YangXiao69/WSPS-325-150K-PEFA/接线图/并柜控制单元/WS2.016.289.V01 WSPS-325-150K-PEFA并柜控制单元接线图 表/WSPS-325-150K-PEFA并柜控制单元接线图.pdf

RPD OPD | DB9 | DB9

J1 J2

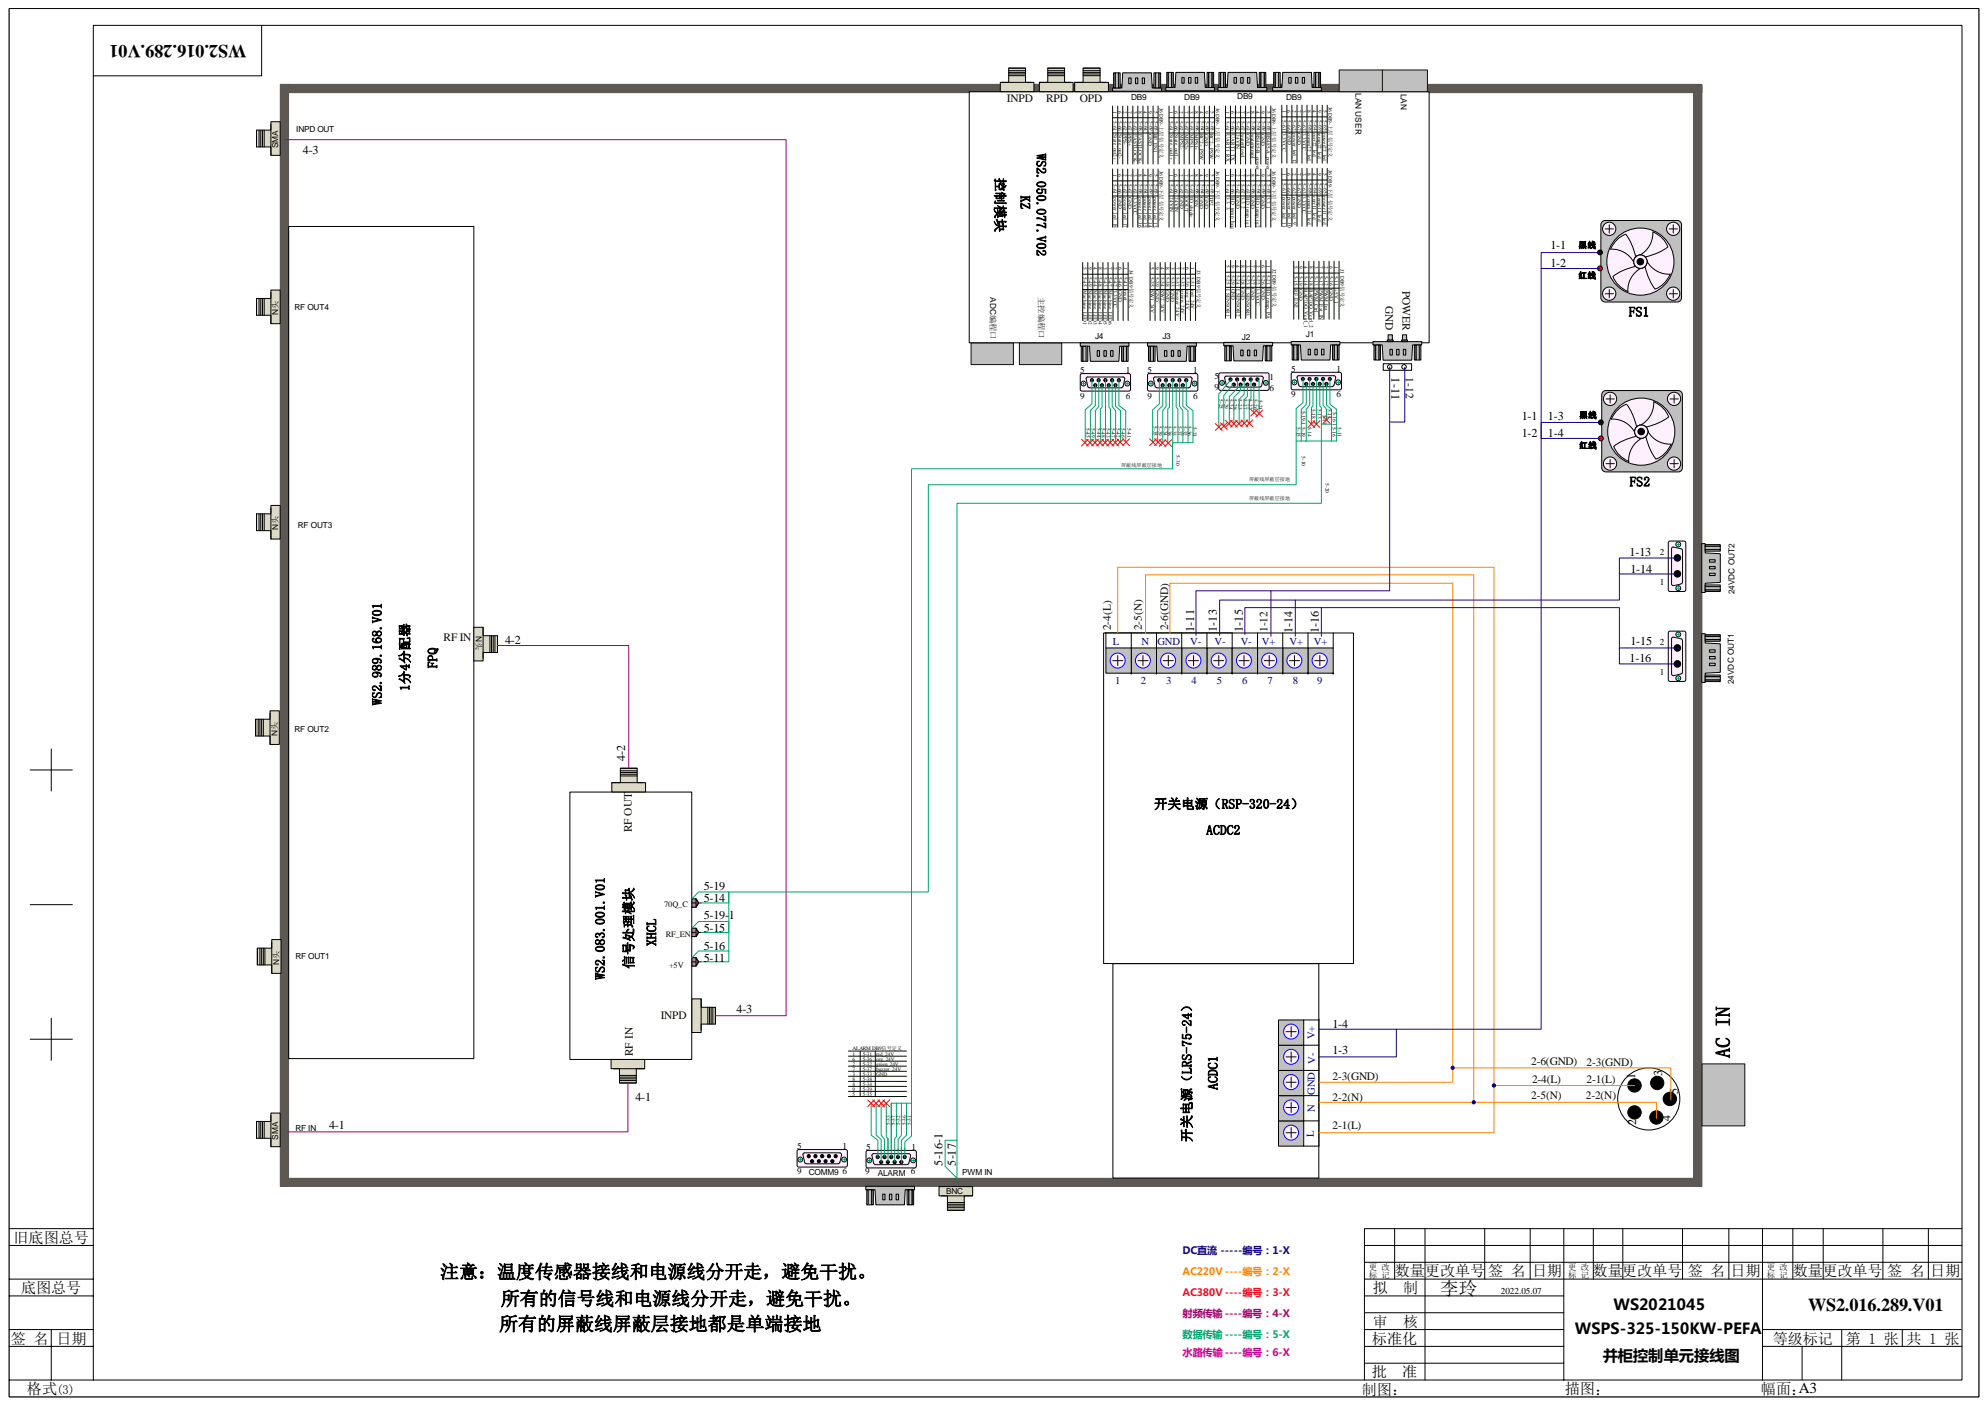
[picture p26: page 1]
旧底图总号; 底图总号; 数量更改单号; 更改单号; 更改单号 签 名; 标准化; 等级标记; 并柜控制单元接线图; WSPS-325-150KW-PEFA; DC直流; 数据传输; 射频传输; 水路传输 ----编号：6-X; 所有的信号线和电源线分开走，避免干扰。; GND; POWER; 5-11 J1 DB9信号定义; BAP70Q_Vctrl_1; BAP70Q_Vctrl_2; PWM_Ctrl; PWM_Ext_IN; PWM_Int; 9876 GND 5-15; I_SENSOR2; I_SENSOR3; 3.3VCC; BD_temp_PA; J2 DB9 信号定义; I_SENSOR1; LAN USER; LAN; 主控编程口; 所有的屏蔽线屏蔽层接地都是单端接地; power_led_12; temp22_led; power22_led; J6 DB9-上层 信号定义 162738495; GND 5-67; comm22_led; power_led_9; temp11_led; power11_led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

头 SMA SMARF IN INPD OUT RF OUT4 RF OUT3 RF OUT2 RF OUT1

注意：温度传感器接线和电源线分开走，避免干扰。
