YangXiao69/WSPS-325-150K-PEFA/接线图/整机/WS2.016.258.V01 WSPS-325-150K-PEFA整机接线图、表/WSPS-325-150K-PEFA整机接线图.pdf

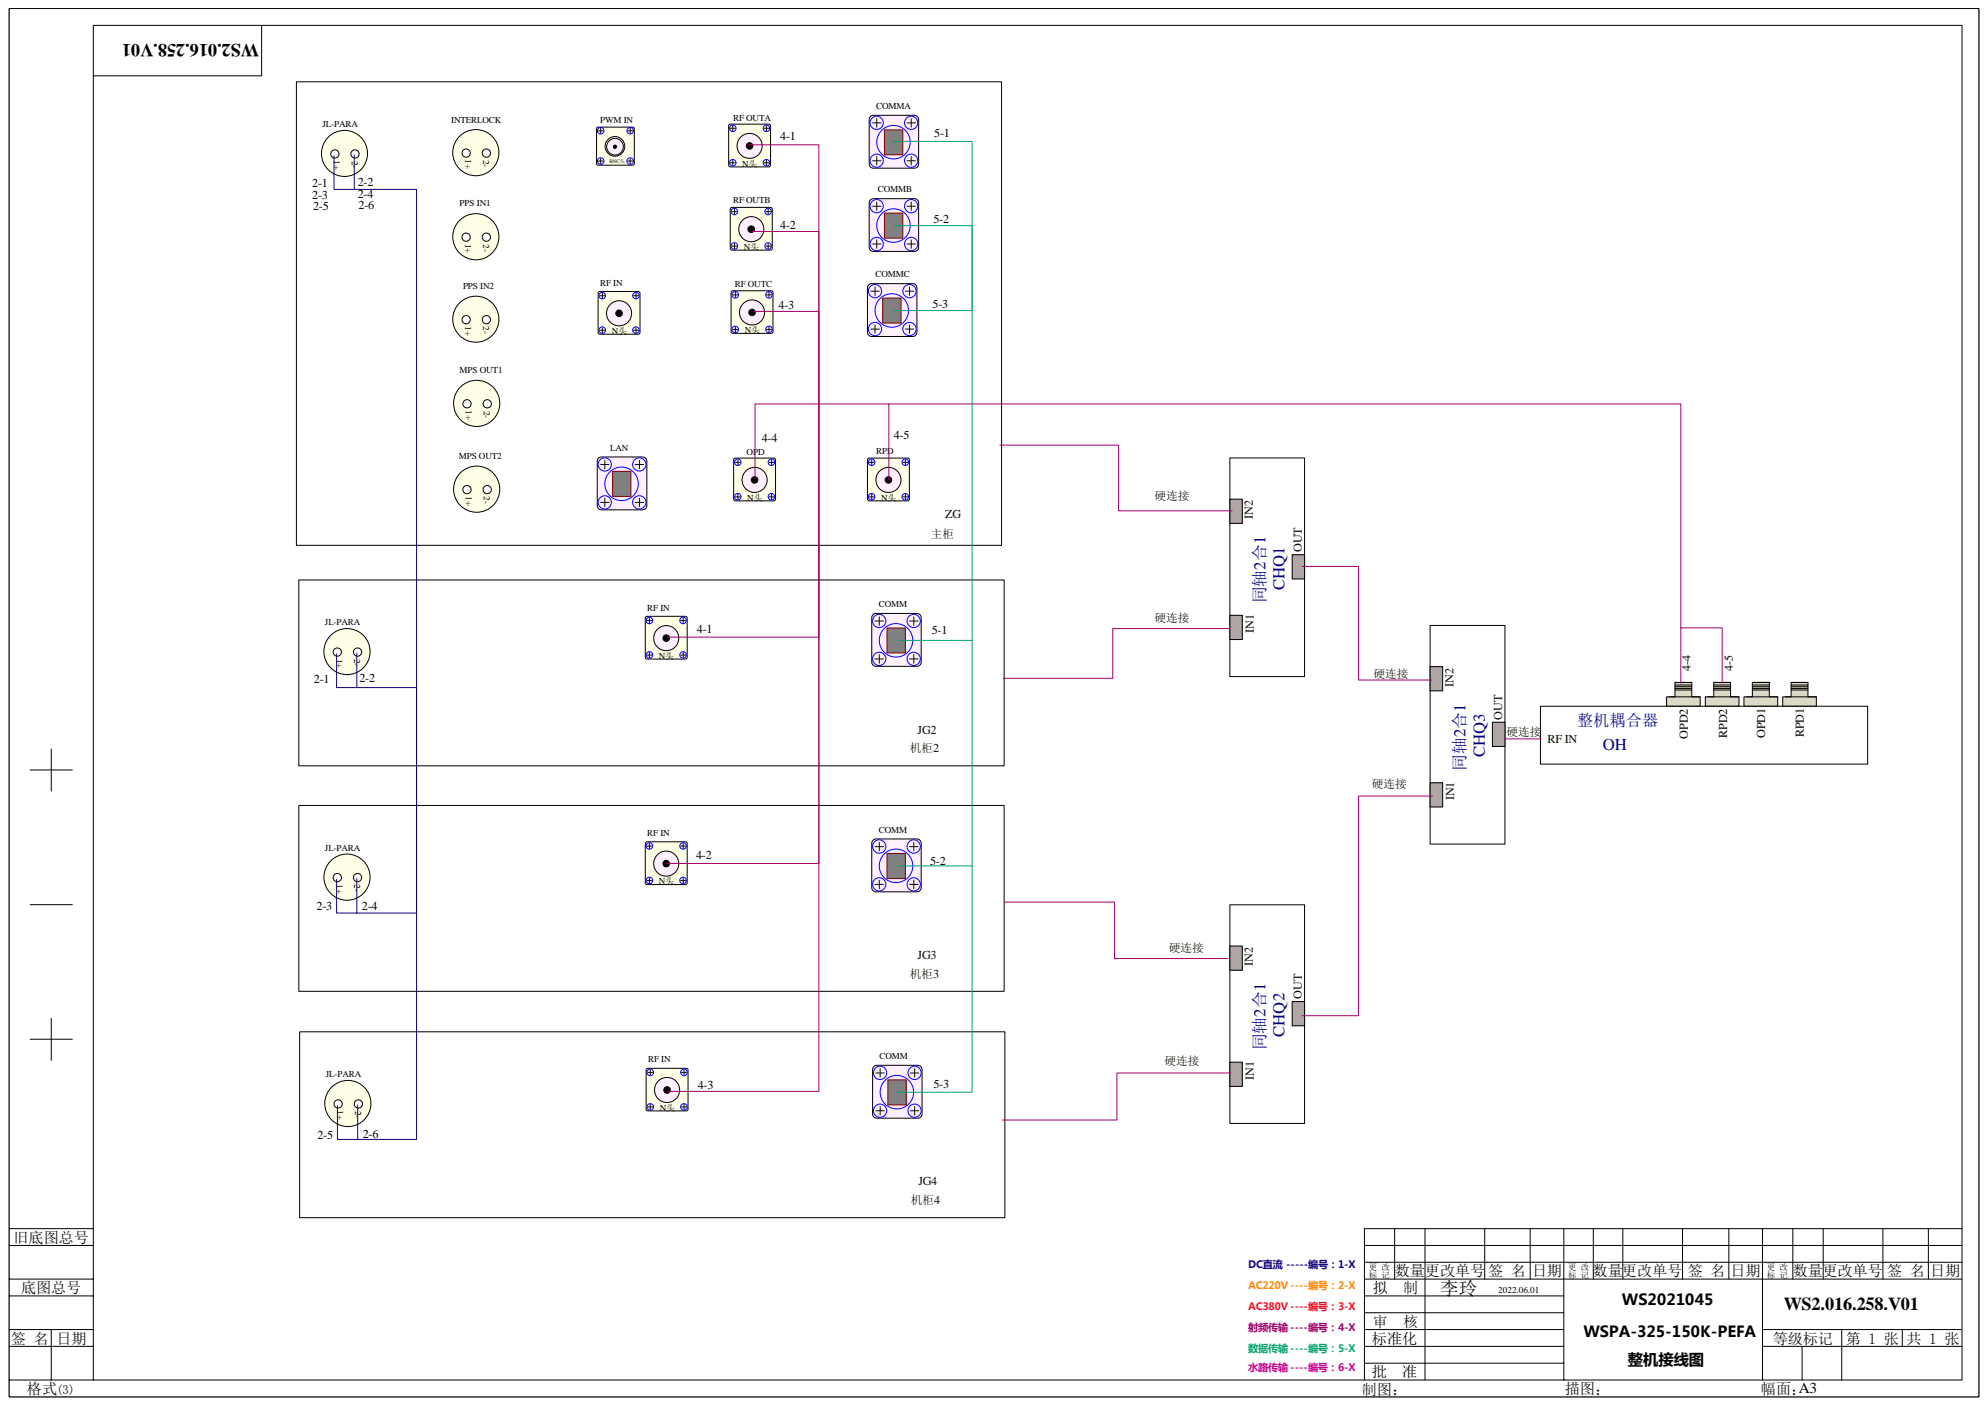
[picture p27: page 1]
旧底图总号; 底图总号; 数量更改单号; 更改单号; 更改单号 签 名; 标准化; 等级标记; DC直流; 数据传输; 射频传输; 水路传输 ----编号：6-X; 整机接线图; WSPA-325-150K-PEFA; INTERLOCK; PPS IN1; PPS IN2; MPS OUT1; MPS OUT2; BNC头; LAN; COMMA; COMMB; COMMC; RF OUTA; RF OUTB; RF OUTC; PWM IN; OPD; RPD; JL-PARA; COMM; CHQ1; OUT; CHQ2; CHQ3; IN1 IN2 整机耦合器 OH OPD2; RPD2; OPD1; RPD1 RF IN; 硬连接
