YangXiao69/WSPS-325-150K-PEFA/接线图/驱动插件/WS2.016.288.V01 WSPS-325-150K-PEFA驱动插件接线图 表/WSPS-325-150K-PEFA驱动插件接线图1.pdf

红线

黑线

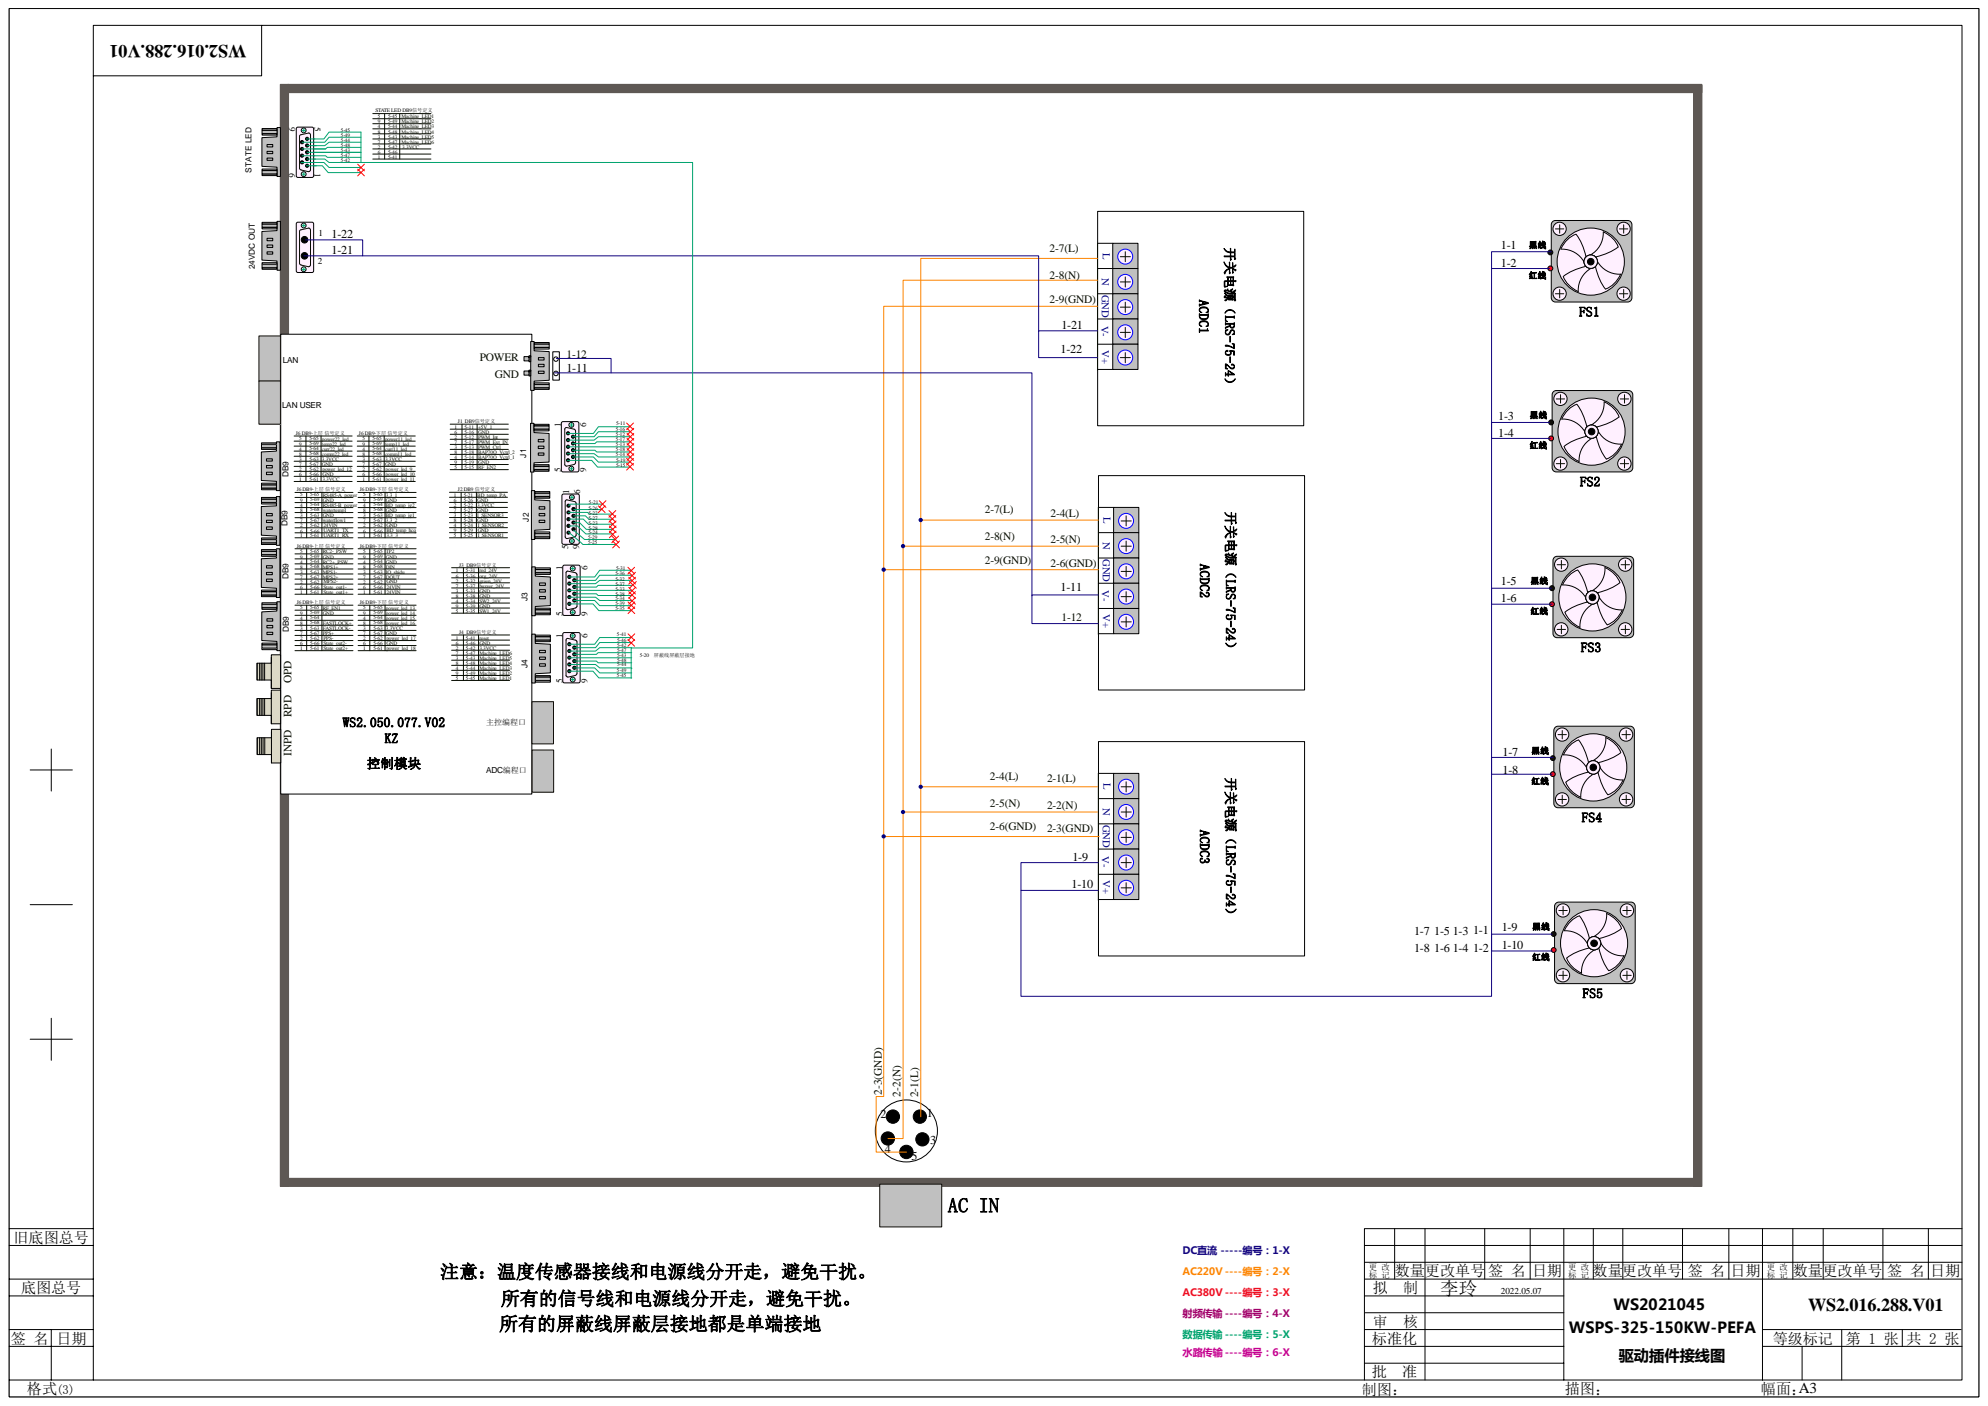
[picture p28: page 1]
旧底图总号; 底图总号; 数量更改单号; 更改单号; 更改单号 签 名; 标准化; 等级标记; 驱动插件接线图; WSPS-325-150KW-PEFA; DC直流; 数据传输; 射频传输; 水路传输 ----编号：6-X; 所有的信号线和电源线分开走，避免干扰。; DB9 DB9 OPD RPD; GND; POWER; J1 DB9信号定义; PWM_Int PWM_Ext_IN PWM_Ctrl; BAP70Q_Vctrl_1; BAP70Q_Vctrl_2; 3.3VCC; I_SENSOR3; BD_temp_PA; I_SENSOR2; J2 DB9 信号定义; I_SENSOR1; LAN; LAN USER; 主控编程口; 24VDC OUT 12; 所有的屏蔽线屏蔽层接地都是单端接地; temp22_led; power22_led; power_led_12; J6 DB9-上层 信号定义; comm22_led; temp11_led; power11_led; power_led_9; J6 DB9-下层 信号定义; power_led_11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

1 6 J6 DB9-上层 信号定义 | 5-61 5-66 | State_out1-State_out1+

5 | 5-65 5-69 | RF_EN1
9 4 3 8 7 6 2 1 | 5-68 5-64 5-63 5-67 5-66 5-62 5-61 | GND FASTLOCK-FASTLOCK+ PPS+ PPS-State_out2-State_out2+

注意：温度传感器接线和电源线分开走，避免干扰。
