YangXiao69/WSPS-325-150K-PEFA/接线图/驱动插件/WS2.016.288.V01 WSPS-325-150K-PEFA驱动插件接线图 表/WSPS-325-150K-PEFA驱动插件接线图2.pdf

## WS2.135.025.V01

## JKMK

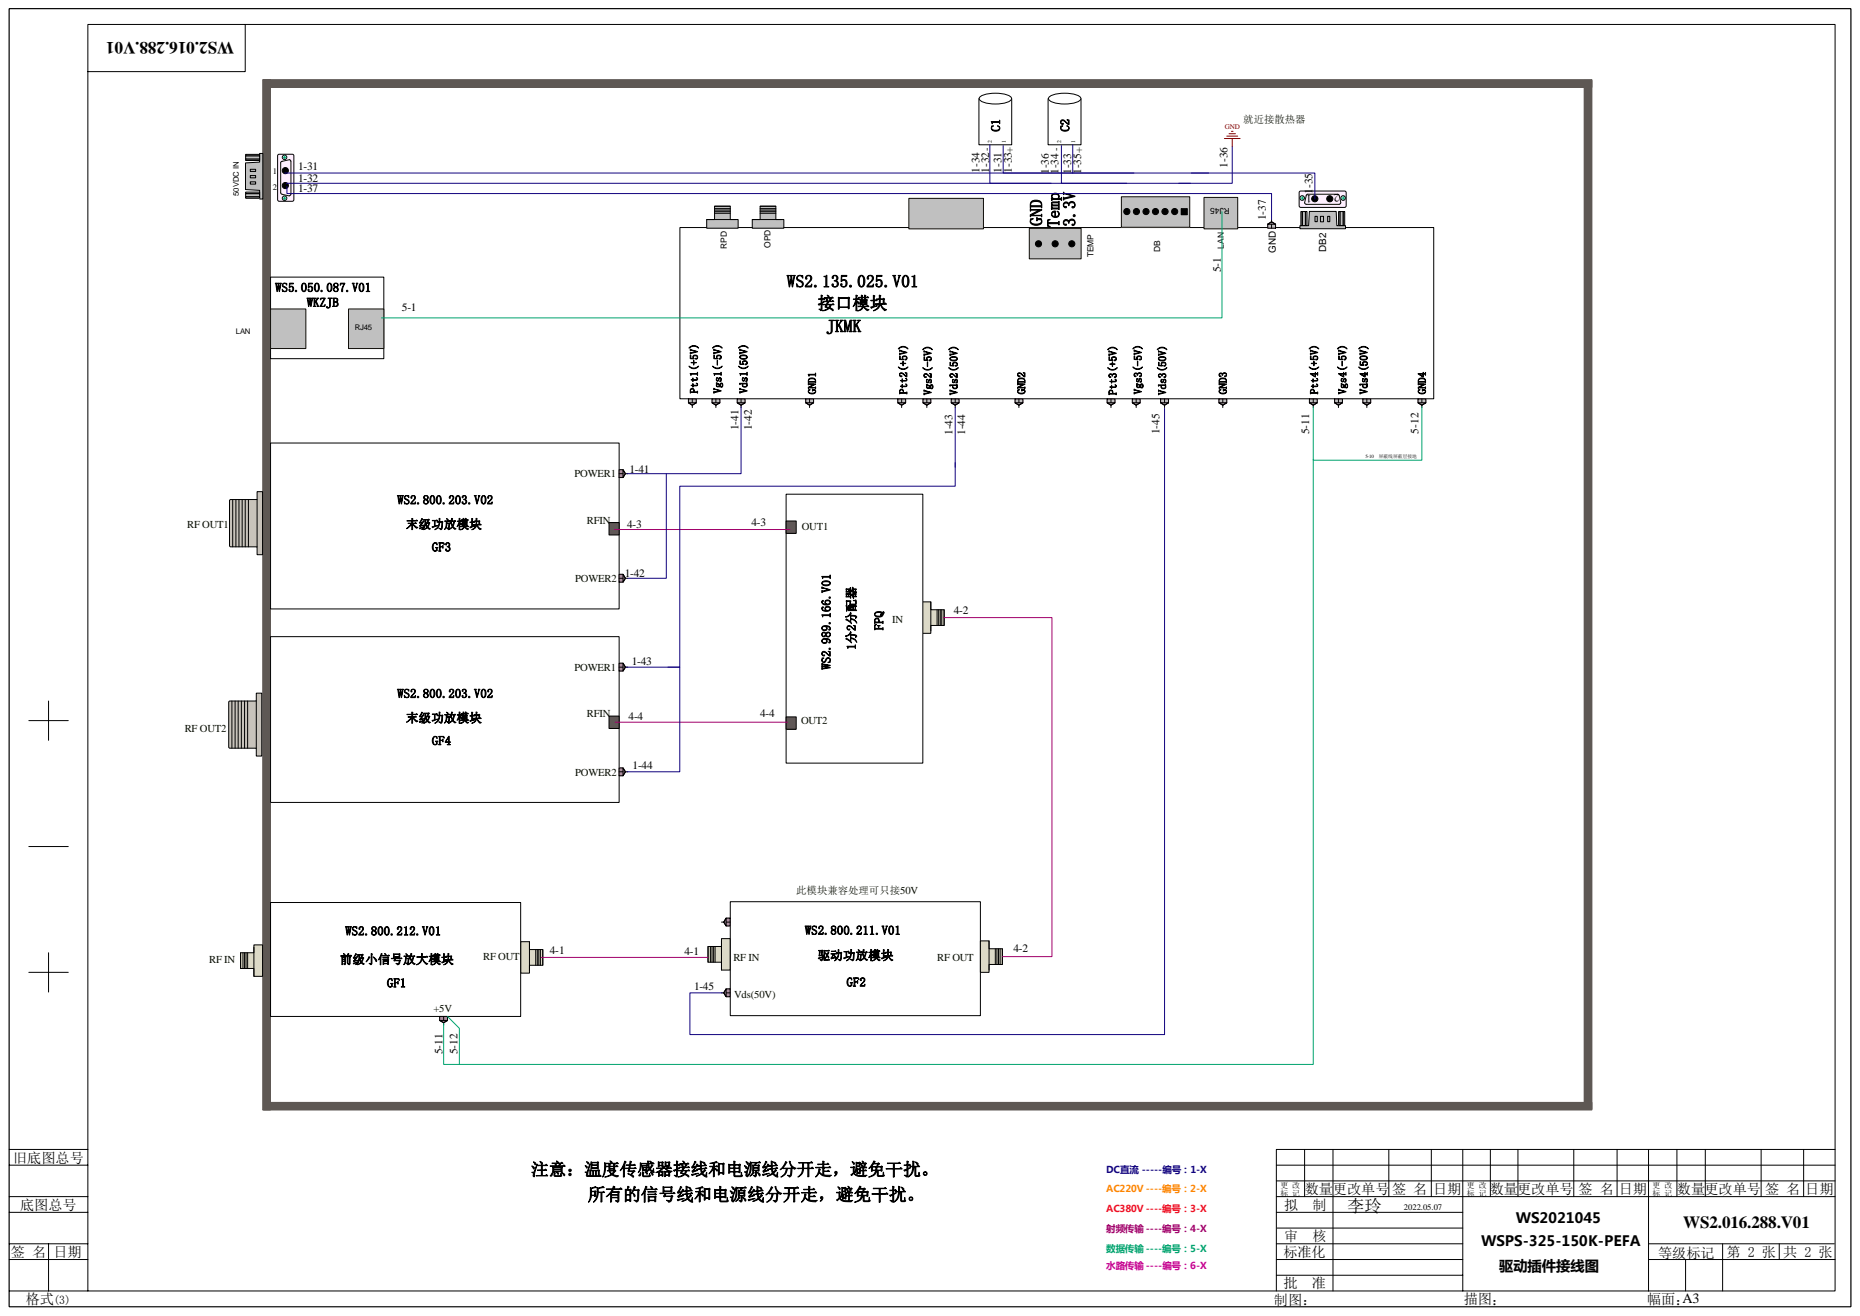
[picture p29: page 1]
旧底图总号; 底图总号; 数量更改单号; 更改单号; 更改单号 签 名; 标准化; 等级标记; WSPS-325-150K-PEFA 驱动插件接线图; DC直流; 数据传输; 射频传输; 水路传输 ----编号：6-X; 所有的信号线和电源线分开走，避免干扰。; RFIN; 末级功放模块; RF OUT1; RF OUT2; POWER1; POWER2; 1分2分配器; 前级小信号放大模块; 驱动功放模块; WKZJB; LAN; RPD; OPD; GND; Temp; Ptt1(+5V); Vgs1(-5V); Vgs2(-5V); Ptt3(+5V); Vgs3(-5V); Ptt4(+5V); Vgs4(-5V); 接口模块; TEMP; Vds1(50V); GND1; Ptt2(+5V); Vds2(50V); GND2; Vds3(50V); GND3; Vds4(50V); GND4; RF OUT; OUT1; OUT2; 就近接散热器; 50VDC IN 12; Vds(50V); 5-10 屏蔽线屏蔽层接地; 此模块兼容处理可只接50V; FPQ

注意：温度传感器接线和电源线分开走，避免干扰。
