YangXiao69/WSPS-325-150K-PEFA/接线图/功放插件/功放插件第一版与第二版共用/WS2.016.268.V01 WSPS-325-150K-PEFA功放插件接线图 一二版可共用/WSPS-325-150K-PEFA功放插件接线图.pdf

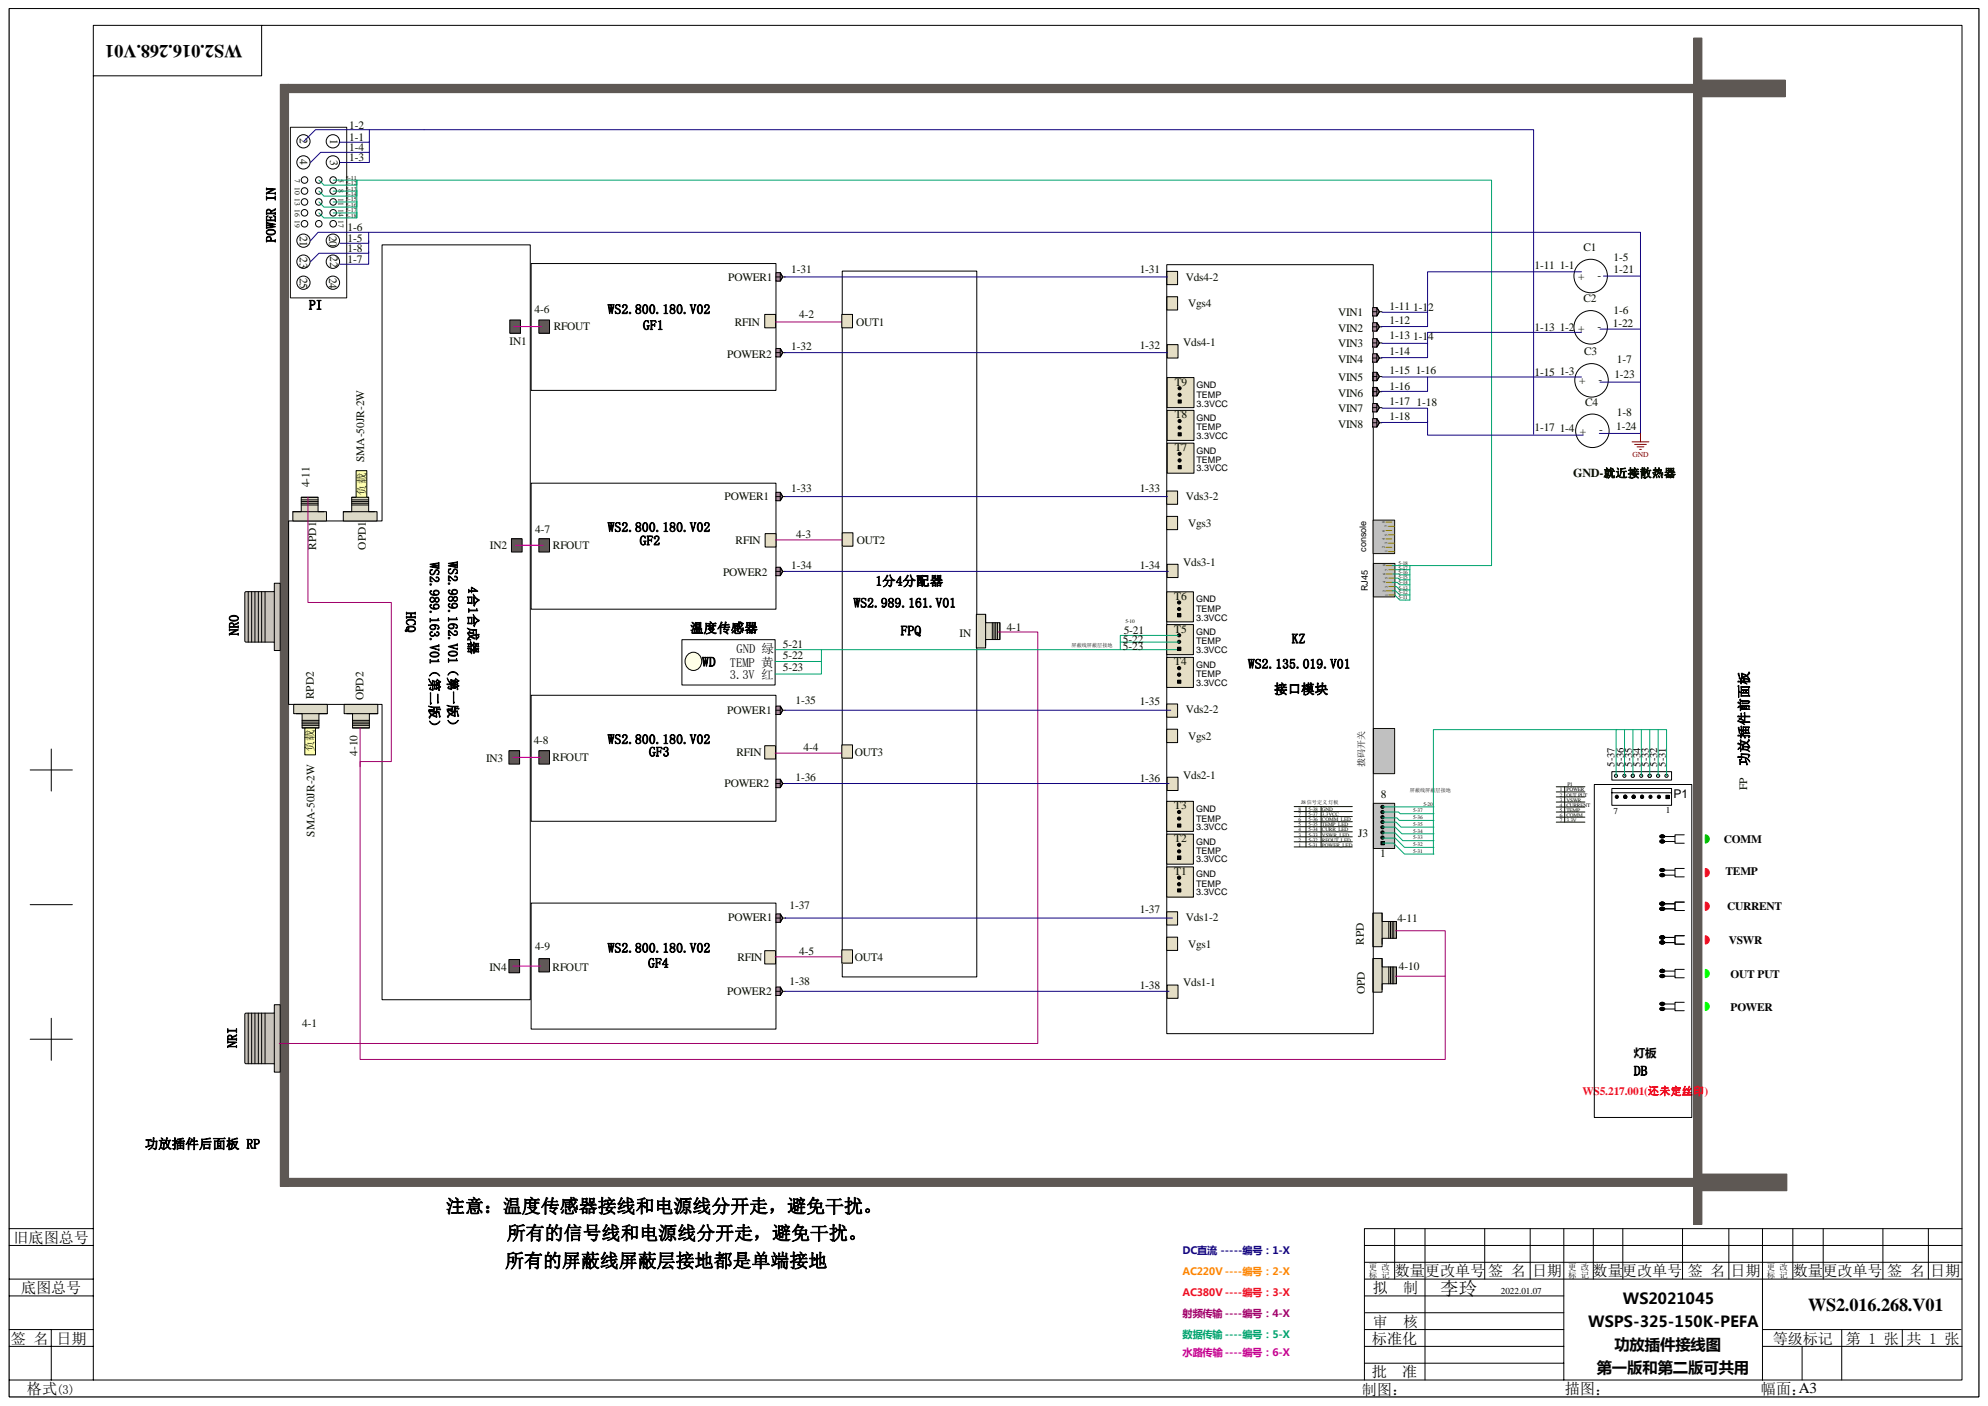
[picture p30: page 1]
旧底图总号; 底图总号; 数量更改单号; 更改单号; 更改单号 签 名; 标准化; 等级标记; 功放插件接线图; DC直流; 数据传输; 射频传输; 水路传输 ----编号：6-X; 所有的信号线和电源线分开走，避免干扰。; 1分4分配器; 4合1合成器; RPD1; OPD1; POWER1; POWER2; NRO; WS2.989.163.V01（第二版） WS2.989.161.V01; RPD2; OPD2; HCQ; FPQ; 功放插件前面板 FP; 功放插件后面板 RP; GND; POWER_LED; VSWR_LED; TEMP_LED; 3.3VCC; RFOUT_LED; COMM_LED; CURR_LED; J8 信号定义 灯板; OPD RPD; TEMP; Vds4-2; Vds4-1; Vgs4; OUT1; OUT2; OUT3; OUT4; RFIN; RFOUT; 接口模块; WSPS-325-150K-PEFA; 所有的屏蔽线屏蔽层接地都是单端接地; VIN5 VIN6; NRI; WS5.217.001(还未定丝印)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

注意：温度传感器接线和电源线分开走，避免干扰。
