YangXiao69/WSPS-325-150K-PEFA/接线图/从柜/WS2.016.287.V01 WSPS-325-150K-PEFA从柜接线图 表/WSPS-325-150K-PEFA从柜接线图-1.pdf

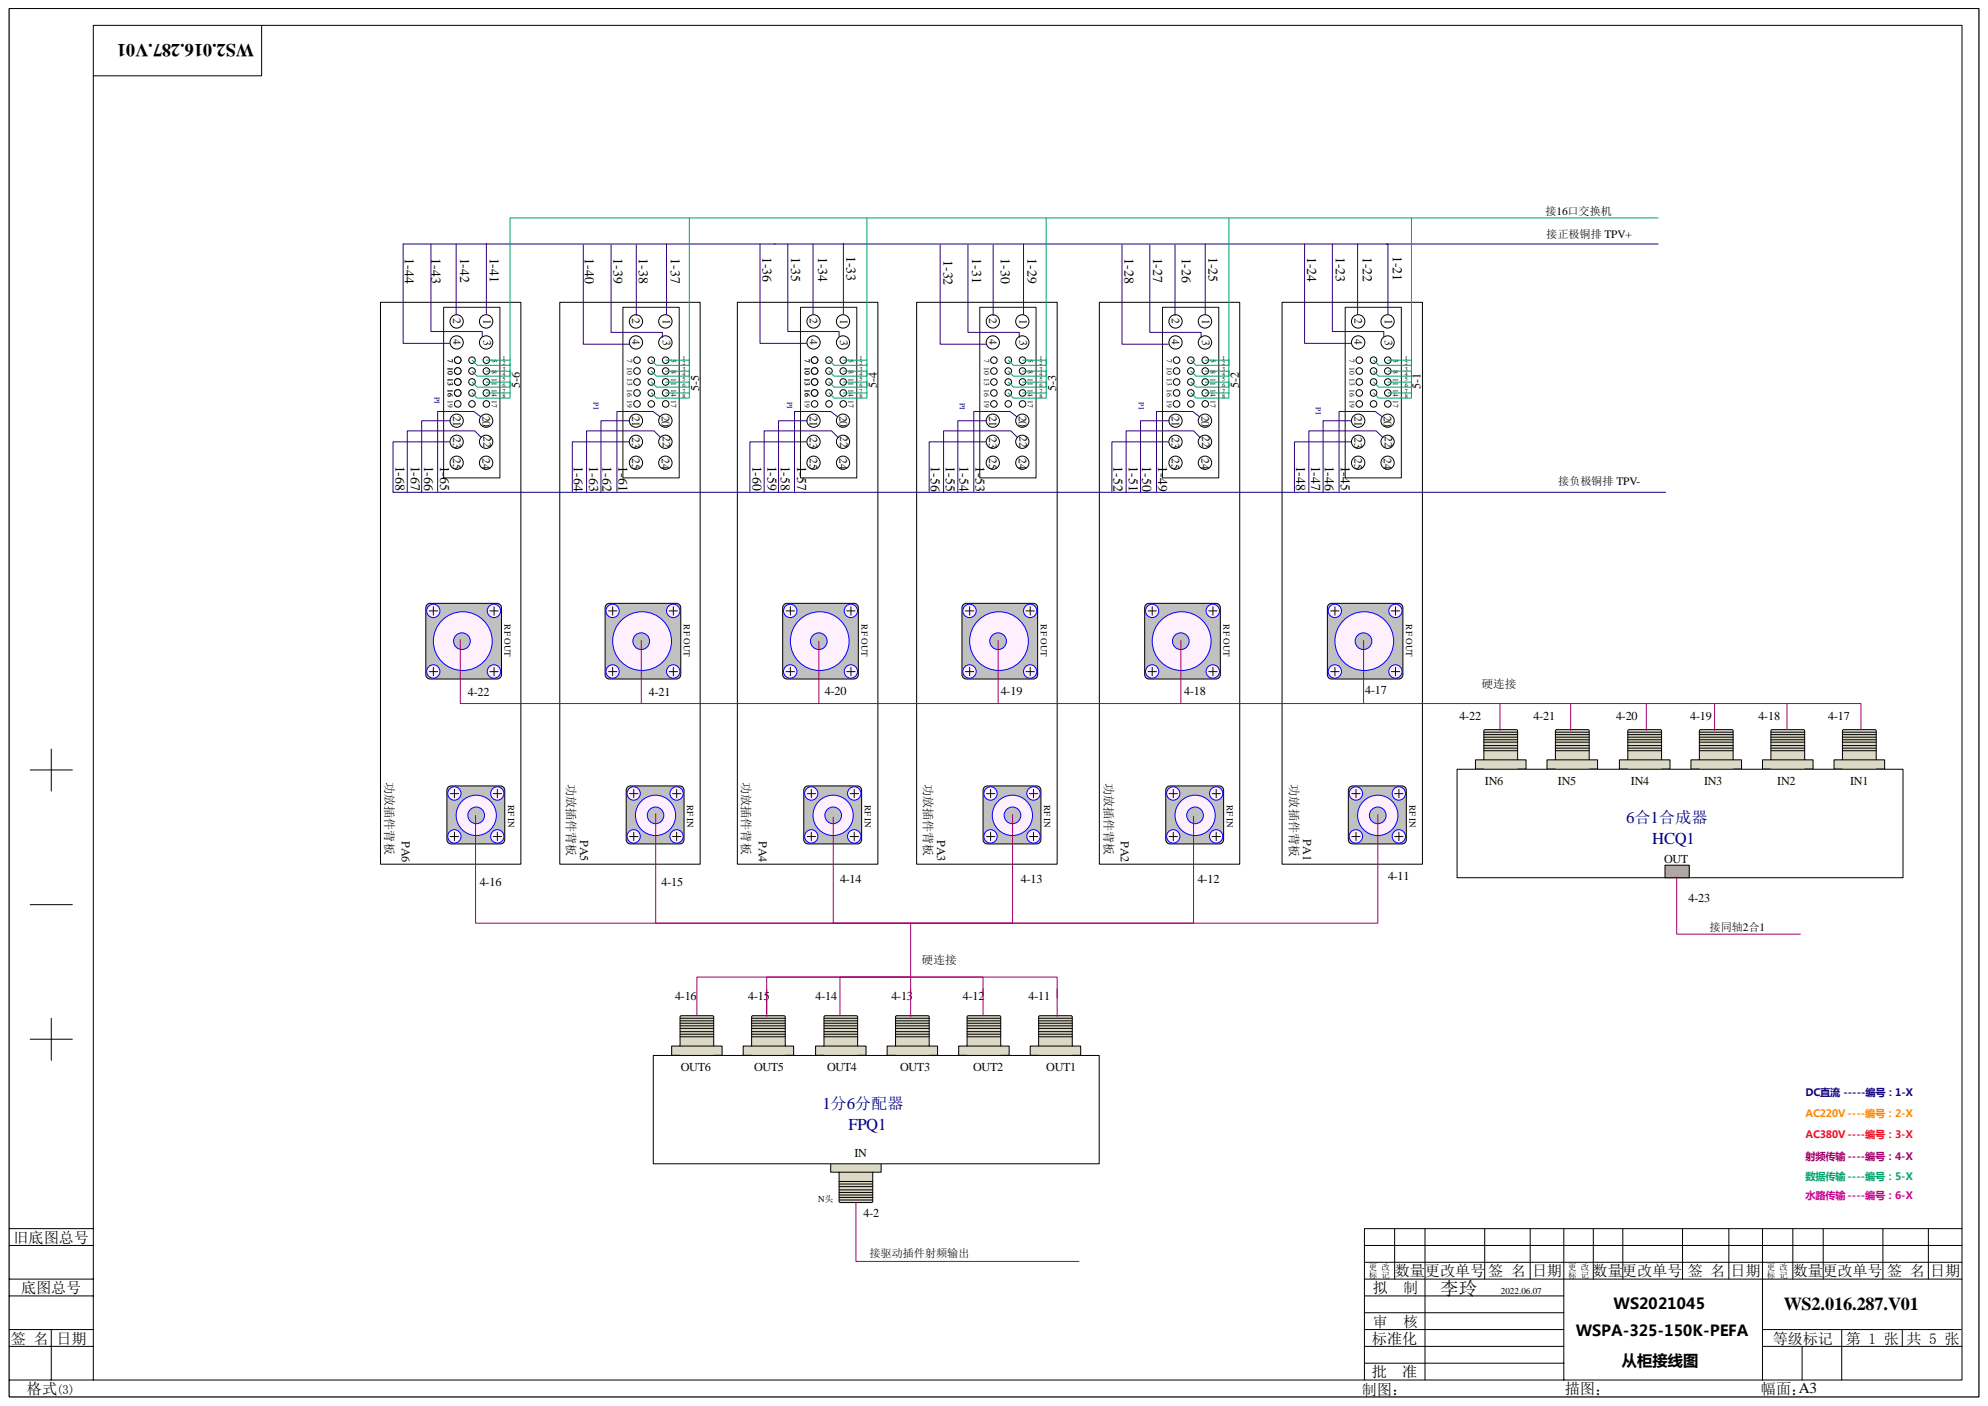
[picture p38: page 1]
旧底图总号; 底图总号; 数量更改单号; 更改单号; 更改单号 签 名; 标准化; 等级标记; DC直流; 数据传输; 射频传输; 水路传输 ----编号：6-X; 功放插件背板; 1分6分配器 FPQ1; OUT6; OUT5; OUT4; OUT3; OUT2; OUT1; 6合1合成器 HCQ1; OUT; 硬连接; 接同轴2合1; 接驱动插件射频输出; 接正极铜排 TPV+; 接负极铜排 TPV-; 接16口交换机; 从柜接线图; WS2021045 WSPA-325-150K-PEFA

RF OUT RF IN
