YangXiao69/WSPS-325-150K-PEFA/接线图/从柜/WS2.016.287.V01 WSPS-325-150K-PEFA从柜接线图 表/WSPS-325-150K-PEFA从柜接线图-3.pdf

P8 | P7 | P6 P5
P12 P11 P10 P9 | V2+

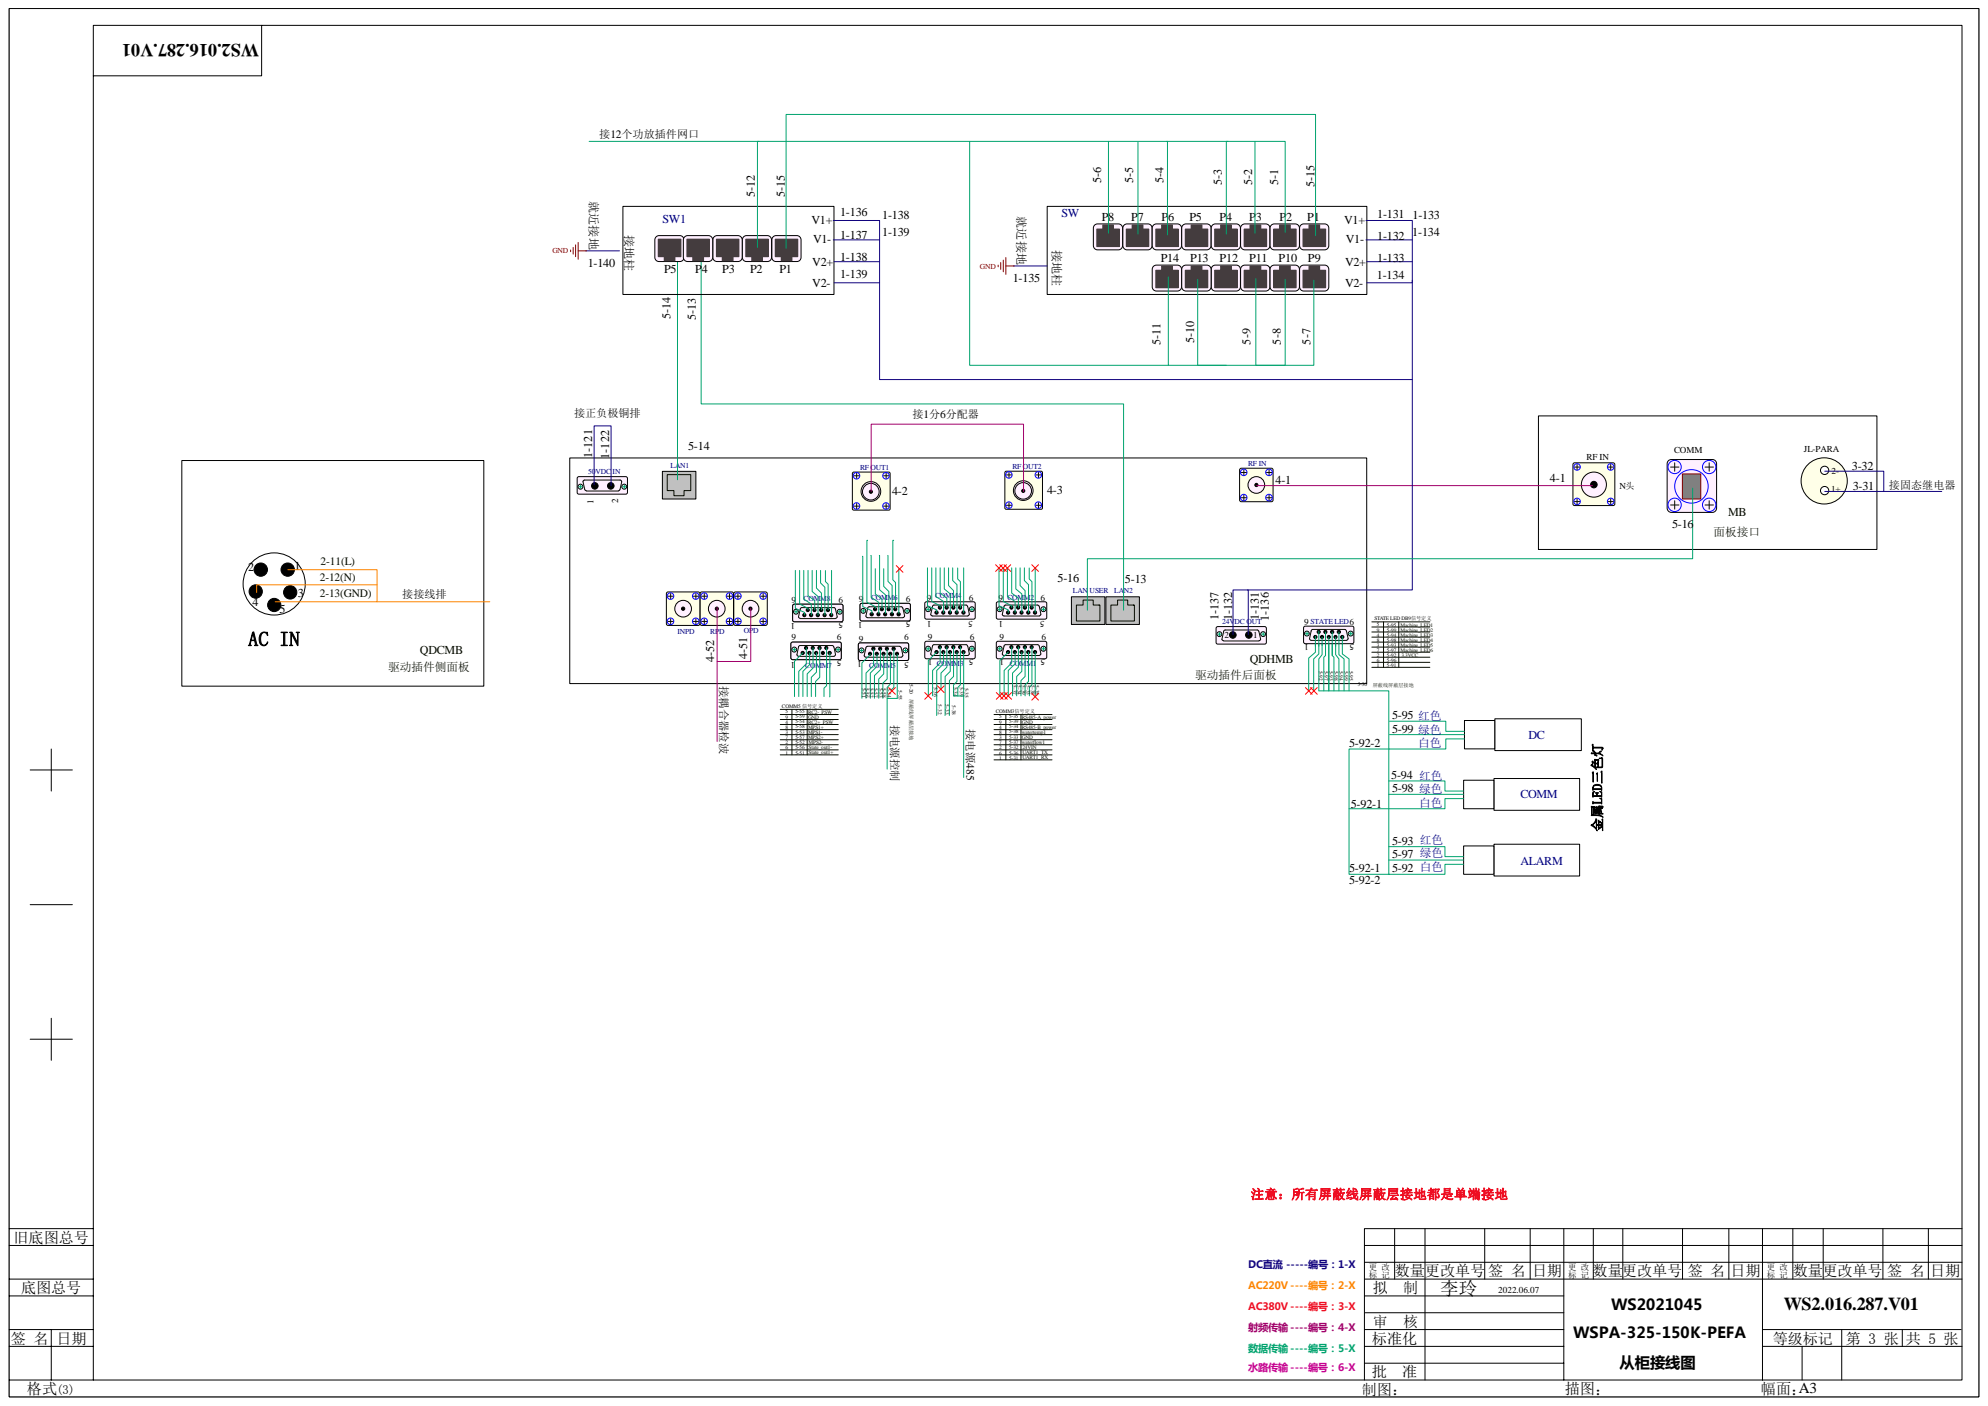
[picture p39: page 1]

5 | 5-95 | Machine_LED1
