YangXiao69/WSPS-325-150K-PEFA/接线图/从柜/WS2.016.287.V01 WSPS-325-150K-PEFA从柜接线图 表/WSPS-325-150K-PEFA从柜接线图-4.pdf

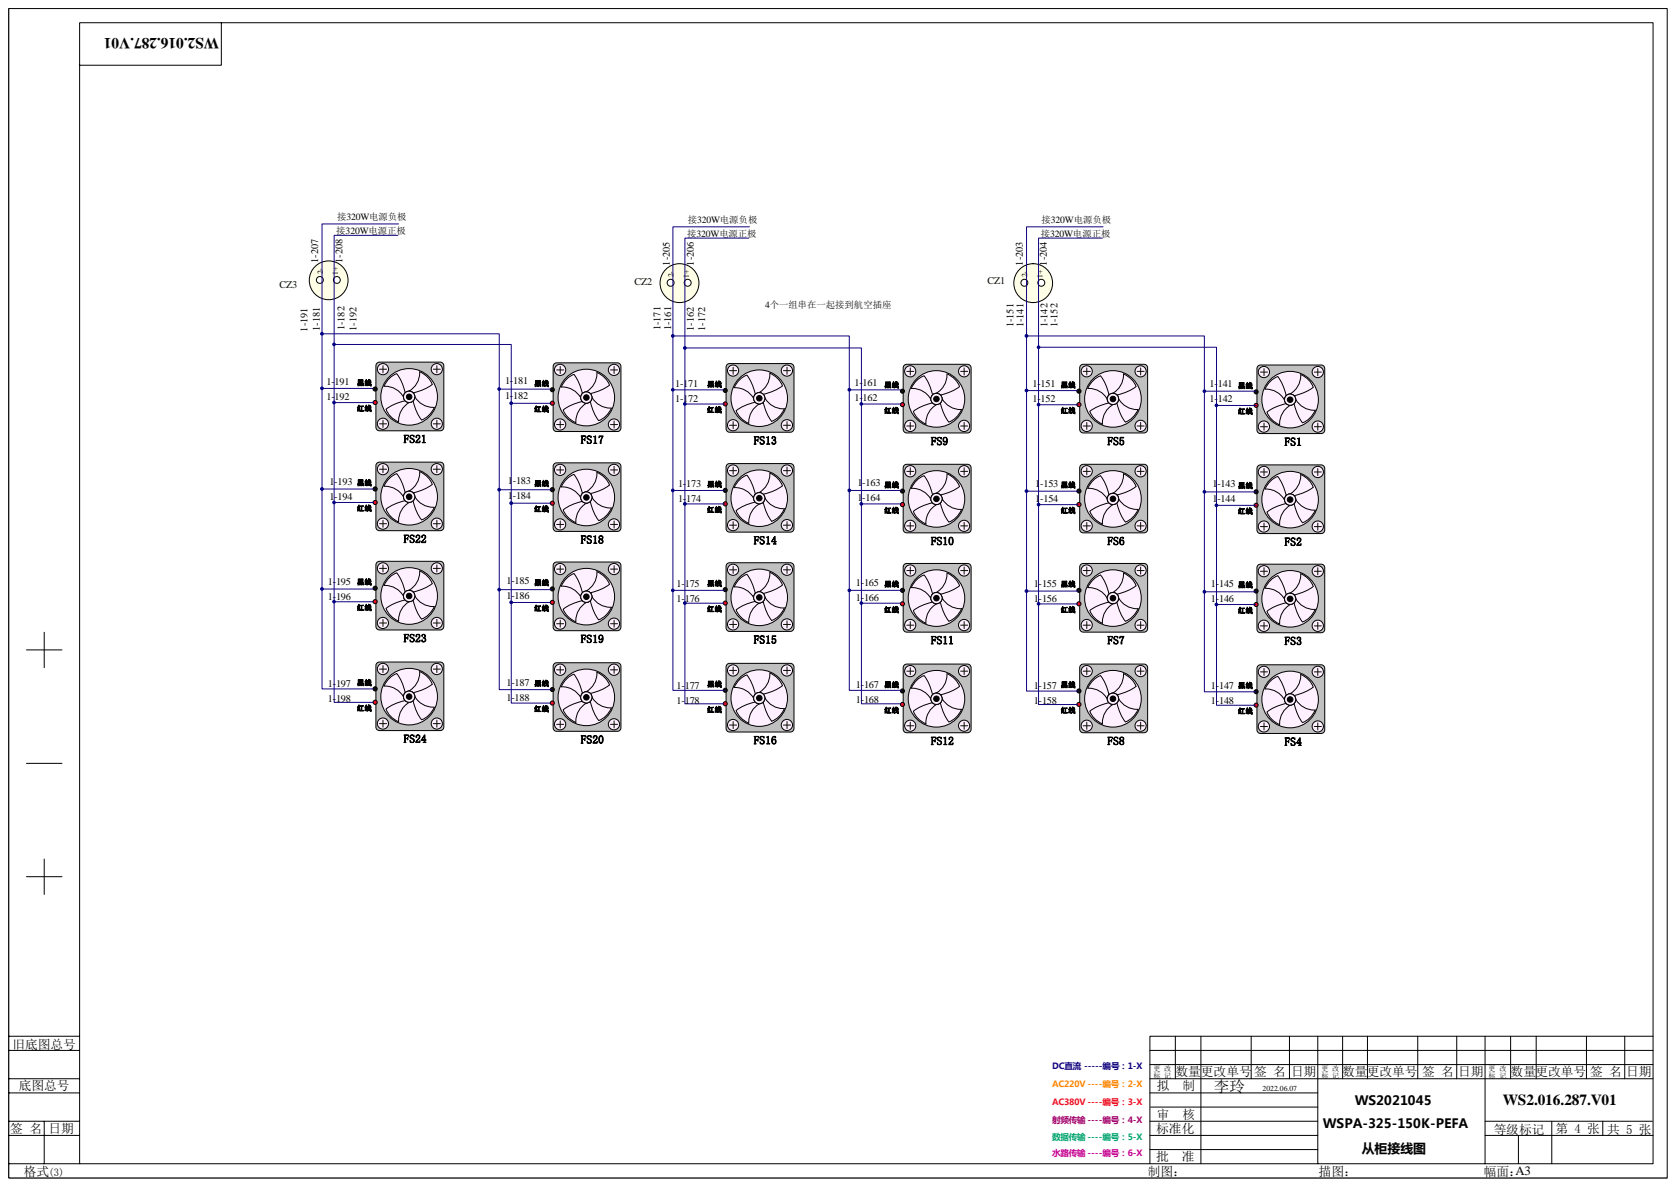
[picture p40: page 1]
旧底图总号; 底图总号; 数量更改单号; 更改单号; 更改单号 签 名; 标准化; 等级标记; DC直流; 数据传输; 射频传输; 水路传输 ----编号：6-X; 接320W电源负极; 接320W电源正极; 4个一组串在一起接到航空插座; 接320W电源负极 接320W电源正极; 从柜接线图; WS2021045 WSPA-325-150K-PEFA
