YangXiao69/WSPS-325-150K-PEFA/接线图/从柜/WS2.016.287.V01 WSPS-325-150K-PEFA从柜接线图 表/WSPS-325-150K-PEFA从柜接线图-电源.pdf

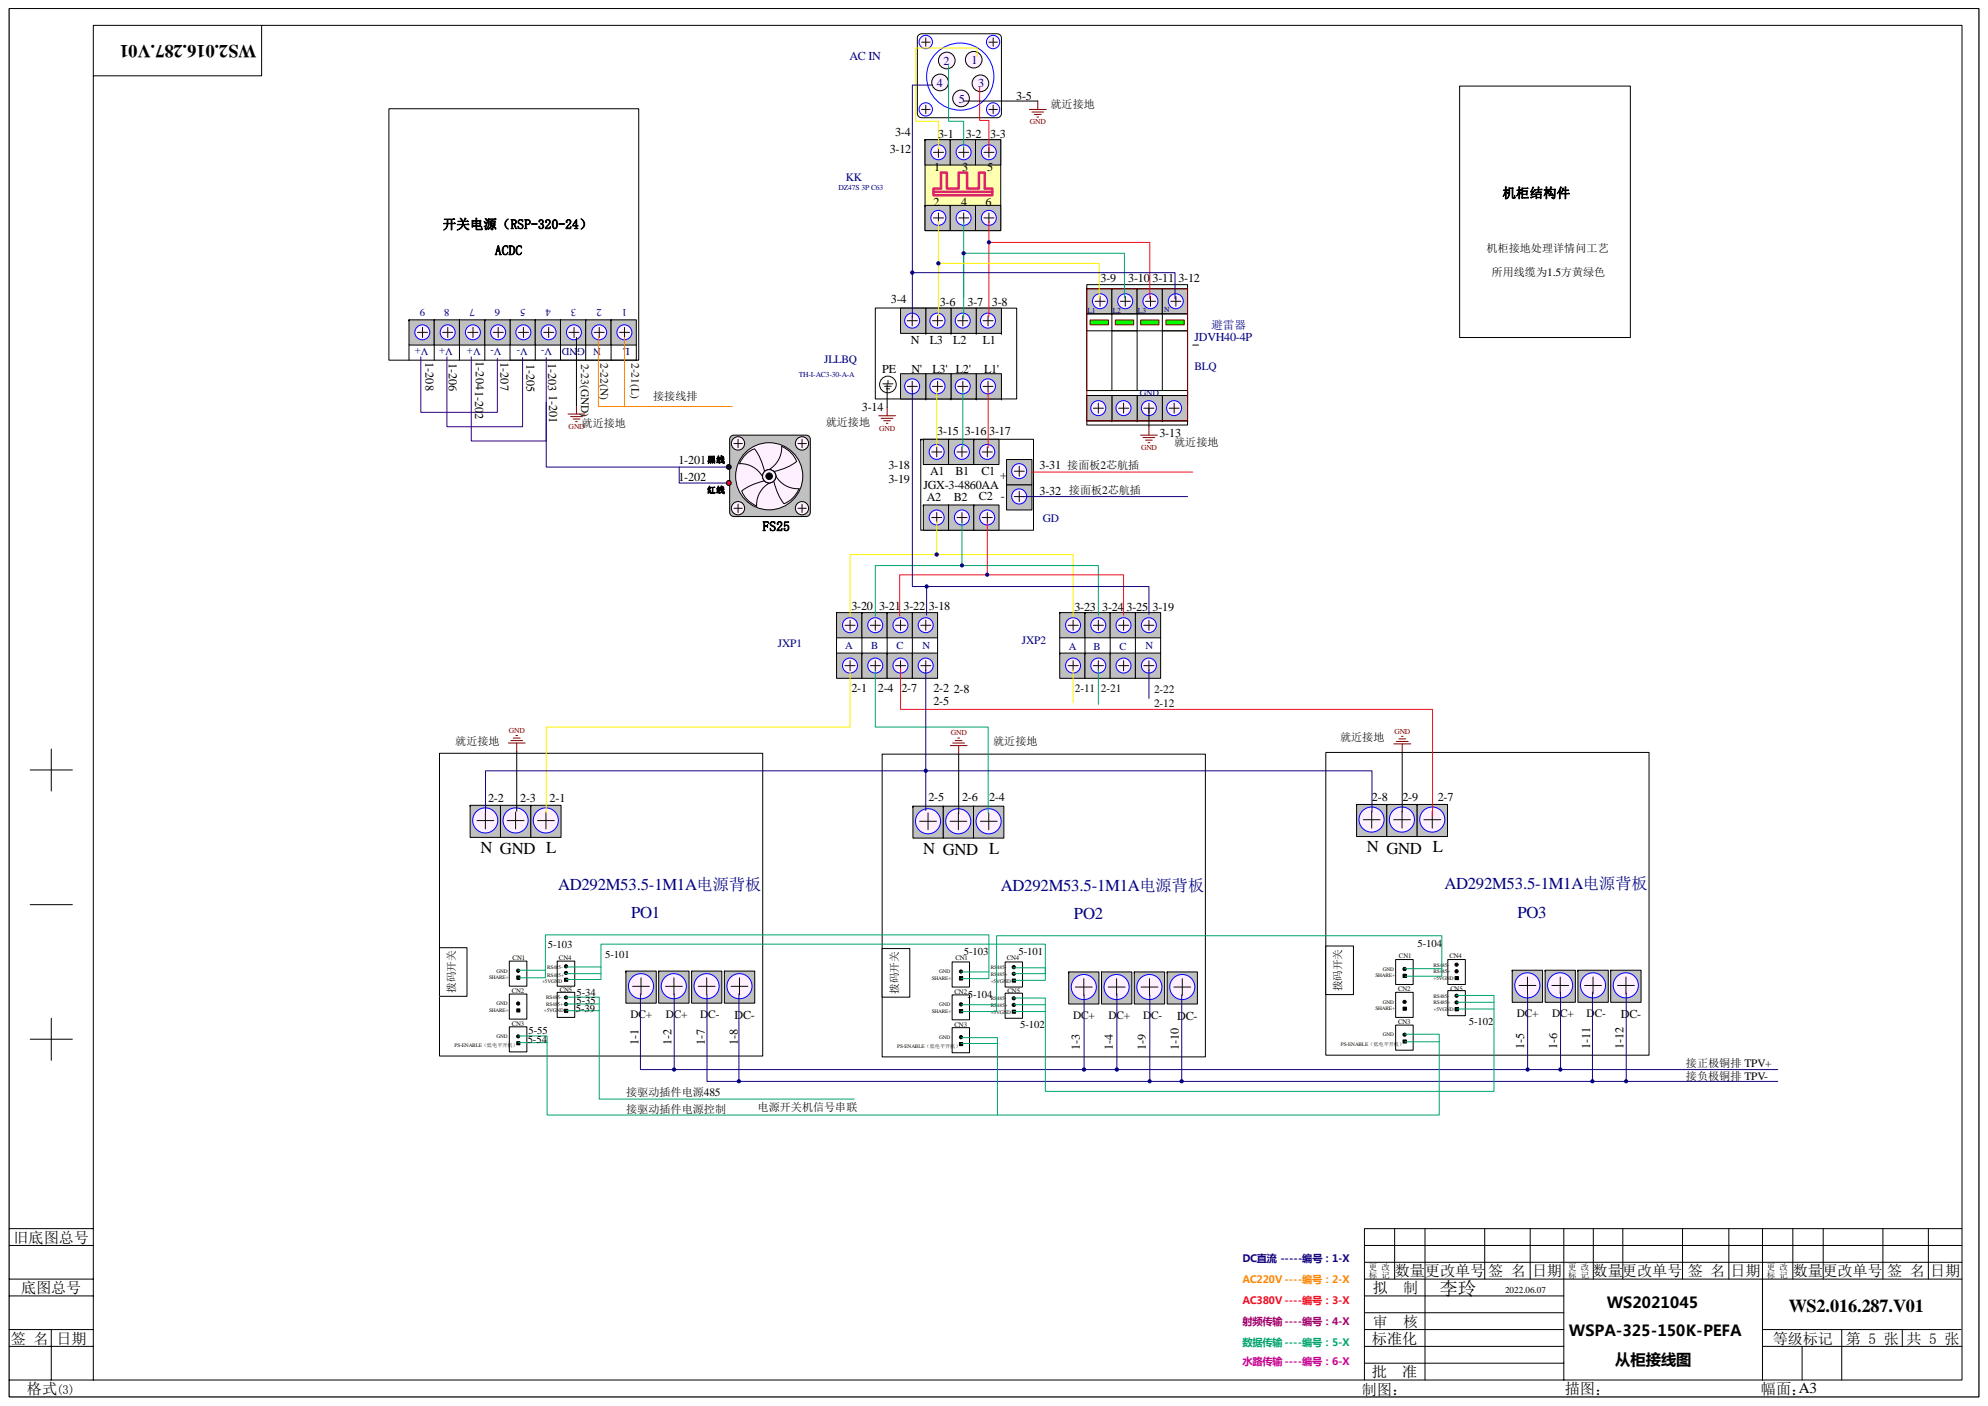
[picture p41: page 1]
