YangXiao69/WSPS-325-150K-PEFA/Software/WSPS-325-150K-PEFA-438-1-V1.0/W5500/socket.c

/**
******************************************************************************
* @file    		Socket.c
* @author  		WIZnet Software Team 
* @version 		V1.0
* @date    		2015-xx-xx
* @brief   		Socket编程相关函数 
******************************************************************************
*/
#include <stdio.h>

#include "./W5500_conf.h"
#include "./socket.h"
#include "./w5500.h"

/**
*@brief   This Socket function initialize the channel in perticular mode, 
					and set the port and wait for W5200 done it.
*@param		s: socket number.
*@param		protocol: The socket to chose.
*@param		port:The port to bind.
*@param		flag: Set some bit of MR,such as **< No Delayed Ack(TCP) flag.
*@return  1 for sucess else 0.
*/
uint8 socket(SOCKET s, uint8 protocol, uint16 port, uint8 flag)
{
    uint8 ret;
    if ( ((protocol&0x0F) == Sn_MR_TCP)    ||
        ((protocol&0x0F) == Sn_MR_UDP)    ||
        ((protocol&0x0F) == Sn_MR_IPRAW)  ||
        ((protocol&0x0F) == Sn_MR_MACRAW) ||
        ((protocol&0x0F) == Sn_MR_PPPOE)   )
    {
        IINCHIP_WRITE( Sn_CR(s) ,Sn_CR_CLOSE);
        while( IINCHIP_READ(Sn_CR(s)));
        IINCHIP_WRITE( Sn_IR(s) , 0xFF);	 /* 关闭socket */
        
        IINCHIP_WRITE(Sn_MR(s) ,protocol | flag);
			
        if (port != 0) {
            IINCHIP_WRITE( Sn_PORT0(s) ,(uint8)((port & 0xff00) >> 8));
            IINCHIP_WRITE( Sn_PORT1(s) ,(uint8)(port & 0x00ff));
        } else {
            local_port++; // if don't set the source port, set local_port number.
            IINCHIP_WRITE(Sn_PORT0(s) ,(uint8)((local_port & 0xff00) >> 8));
            IINCHIP_WRITE(Sn_PORT1(s) ,(uint8)(local_port & 0x00ff));
        }
      IINCHIP_WRITE( Sn_CR(s) ,Sn_CR_OPEN); // run sockinit Sn_CR

      while( IINCHIP_READ(Sn_CR(s)) );
      ret = 1;
   }
   else
      ret = 0;
   return ret;
}


uint8 socket_top(SOCKET s, uint8 protocol, uint16 port, uint8 flag)
{
    uint8 ret;
    if(((protocol&0x0F) == Sn_MR_TCP)     ||
        ((protocol&0x0F) == Sn_MR_UDP)    ||
        ((protocol&0x0F) == Sn_MR_IPRAW)  ||
        ((protocol&0x0F) == Sn_MR_MACRAW) ||
        ((protocol&0x0F) == Sn_MR_PPPOE))
    {
        
        IINCHIP_WRITE_TOP( Sn_CR(s) ,Sn_CR_CLOSE);
        while( IINCHIP_READ_TOP(Sn_CR(s) ) )
                ;/* ------- */
        IINCHIP_WRITE_TOP( Sn_IR(s) , 0xFF);	 /* all clear */	 
        
        
        IINCHIP_WRITE_TOP(Sn_MR(s) ,protocol | flag);
			
      if (port != 0) {
         IINCHIP_WRITE_TOP( Sn_PORT0(s) ,(uint8)((port & 0xff00) >> 8));
         IINCHIP_WRITE_TOP( Sn_PORT1(s) ,(uint8)(port & 0x00ff));
      } 
//			else {  
//         local_port++; // if don't set the source port, set local_port number.
//         IINCHIP_WRITE_TOP(Sn_PORT0(s) ,(uint8)((local_port & 0xff00) >> 8));
//         IINCHIP_WRITE_TOP(Sn_PORT1(s) ,(uint8)(local_port & 0x00ff));
//      }
			
      IINCHIP_WRITE_TOP( Sn_CR(s) ,Sn_CR_OPEN);   // run sockinit Sn_CR

      while( IINCHIP_READ_TOP(Sn_CR(s)));		
      ret = 1;   
   }
   else
      ret = 0;
   return ret;
}

/**
*@brief   This function close the socket and parameter is "s" which represent the socket number
*@param		s: socket number.
*@return  None
*/
void close(SOCKET s)
{

    IINCHIP_WRITE( Sn_CR(s) ,Sn_CR_CLOSE);
    
    /* wait to process the command... */
    while( IINCHIP_READ(Sn_CR(s) ) )
        ;/* ------- */
    
    IINCHIP_WRITE( Sn_IR(s) , 0xFF);	 /* all clear */
}

void close_TOP(SOCKET s)
{

    IINCHIP_WRITE_TOP( Sn_CR(s) ,Sn_CR_CLOSE);
    
    /* wait to process the command... */
    while( IINCHIP_READ_TOP(Sn_CR(s) ) )
        ;/* ------- */
    
    IINCHIP_WRITE_TOP( Sn_IR(s) , 0xFF);	 /* all clear */
}


/**
*@brief   This function established  the connection for the channel in passive (server) mode. 
					This function waits for the request from the peer.
*@param		s: socket number.
*@return  1 for success else 0.
*/
uint8 listen(SOCKET s)
{
    uint8 ret;
    if (IINCHIP_READ( Sn_SR(s) ) == SOCK_INIT)
    {
        IINCHIP_WRITE( Sn_CR(s) ,Sn_CR_LISTEN);
        /* wait to process the command... */
        while( IINCHIP_READ(Sn_CR(s) ) )
            ;
        /* ------- */
        ret = 1;
    }
    else
    {
        ret = 0;
    }
    return ret;
}

uint8 listen_TOP(SOCKET s)
{
   uint8 ret;
   if (IINCHIP_READ_TOP( Sn_SR(s) ) == SOCK_INIT)
   {
      IINCHIP_WRITE_TOP( Sn_CR(s) ,Sn_CR_LISTEN);
      /* wait to process the command... */
      while( IINCHIP_READ_TOP(Sn_CR(s) ) )
         ;
      /* ------- */
      ret = 1;
   }
   else
   {
      ret = 0;
   }
   return ret;
}


/**
*@brief		This function established  the connection for the channel in Active (client) mode.
					This function waits for the untill the connection is established.
*@param		s: socket number.
*@param		addr: The server IP address to connect
*@param		port: The server IP port to connect
*@return  1 for success else 0.
*/
uint8 connect(SOCKET s, uint8 * addr, uint16 port)
{
    uint8 ret;
    if(
        ((addr[0] == 0xFF) && (addr[1] == 0xFF) && (addr[2] == 0xFF) && (addr[3] == 0xFF)) ||
        ((addr[0] == 0x00) && (addr[1] == 0x00) && (addr[2] == 0x00) && (addr[3] == 0x00)) ||
        (port == 0x00)
        )
    {
        ret = 0;
    }
    else
    {
        ret = 1;
        // set destination IP
        IINCHIP_WRITE( Sn_DIPR0(s), addr[0]);
        IINCHIP_WRITE( Sn_DIPR1(s), addr[1]);
        IINCHIP_WRITE( Sn_DIPR2(s), addr[2]);
        IINCHIP_WRITE( Sn_DIPR3(s), addr[3]);
        IINCHIP_WRITE( Sn_DPORT0(s), (uint8)((port & 0xff00) >> 8));
        IINCHIP_WRITE( Sn_DPORT1(s), (uint8)(port & 0x00ff));
        IINCHIP_WRITE( Sn_CR(s) ,Sn_CR_CONNECT);
        /* wait for completion */
        while ( IINCHIP_READ(Sn_CR(s) ) ) ;

        while ( IINCHIP_READ(Sn_SR(s)) != SOCK_SYNSENT )
        {
            if(IINCHIP_READ(Sn_SR(s)) == SOCK_ESTABLISHED)
            {
                break;
            }
            if (getSn_IR(s) & Sn_IR_TIMEOUT)
            {
                IINCHIP_WRITE(Sn_IR(s), (Sn_IR_TIMEOUT));  // clear TIMEOUT Interrupt
                ret = 0;
                break;
            }
        }
    }

   return ret;
}

uint8 connect_Top(SOCKET s, uint8 * addr, uint16 port)
{
    uint8 ret;
    if
        (
            ((addr[0] == 0xFF) && (addr[1] == 0xFF) && (addr[2] == 0xFF) && (addr[3] == 0xFF)) ||
            ((addr[0] == 0x00) && (addr[1] == 0x00) && (addr[2] == 0x00) && (addr[3] == 0x00)) ||
            (port == 0x00)
        )
    {
      ret = 0;
    }
    else
    {
        ret = 1;
        // set destination IP
        IINCHIP_WRITE_TOP( Sn_DIPR0(s), addr[0]);
        IINCHIP_WRITE_TOP( Sn_DIPR1(s), addr[1]);
        IINCHIP_WRITE_TOP( Sn_DIPR2(s), addr[2]);
        IINCHIP_WRITE_TOP( Sn_DIPR3(s), addr[3]);
        IINCHIP_WRITE_TOP( Sn_DPORT0(s), (uint8)((port & 0xff00) >> 8));
        IINCHIP_WRITE_TOP( Sn_DPORT1(s), (uint8)(port & 0x00ff));
        IINCHIP_WRITE_TOP( Sn_CR(s) ,Sn_CR_CONNECT);
        /* wait for completion */
        while ( IINCHIP_READ_TOP(Sn_CR(s) ) ) ;

        while ( IINCHIP_READ_TOP(Sn_SR(s)) != SOCK_SYNSENT )
        {
            if(IINCHIP_READ_TOP(Sn_SR(s)) == SOCK_ESTABLISHED)
            {
                break;
            }
//            if (getSn_IR(s) & Sn_IR_TIMEOUT)
            if (IINCHIP_READ_TOP(Sn_IR(s)) & Sn_IR_TIMEOUT)							
            {
                IINCHIP_WRITE_TOP(Sn_IR(s), (Sn_IR_TIMEOUT));  // clear TIMEOUT Interrupt
                ret = 0;
                break;
            }
        }
    }

   return ret;
}

/**
*@brief   This function used for disconnect the socket s
*@param		s: socket number.
*@return  1 for success else 0.
*/
void disconnect(SOCKET s)
{
   IINCHIP_WRITE( Sn_CR(s) ,Sn_CR_DISCON);

   /* wait to process the command... */
   while( IINCHIP_READ(Sn_CR(s) ) )
      ;
   /* ------- */
}

/**
*@brief   This function used to send the data in TCP mode
*@param		s: socket number.
*@param		buf: data buffer to send.
*@param		len: data length.
*@return  1 for success else 0.
*/
uint16 send(SOCKET s, const uint8 * buf, uint16 len)
{
    uint8 status=0;
    uint16 ret=0;
    uint16 freesize=0;
    
    if (len > getIINCHIP_TxMAX(s)) ret = getIINCHIP_TxMAX(s); // check size not to exceed MAX size.
    else ret = len;
    
    // if freebuf is available, start.
    do
    {
        freesize = getSn_TX_FSR(s);
        status = IINCHIP_READ(Sn_SR(s));
        if ((status != SOCK_ESTABLISHED) && (status != SOCK_CLOSE_WAIT))
        {
        ret = 0;
        break;
        }
    } while (freesize < ret);
    
    // copy data
    send_data_processing(s, (uint8 *)buf, ret);
    IINCHIP_WRITE( Sn_CR(s) ,Sn_CR_SEND);
    
    /* wait to process the command... */
    while( IINCHIP_READ(Sn_CR(s) ) );
    
    while ( (IINCHIP_READ(Sn_IR(s) ) & Sn_IR_SEND_OK) != Sn_IR_SEND_OK )
    {
        status = IINCHIP_READ(Sn_SR(s));
        if ((status != SOCK_ESTABLISHED) && (status != SOCK_CLOSE_WAIT) )
        {
        close(s);
        return 0;
        }
    }
    IINCHIP_WRITE( Sn_IR(s) , Sn_IR_SEND_OK);

#ifdef __DEF_IINCHIP_INT__
   putISR(s, getISR(s) & (~Sn_IR_SEND_OK));
#else
   IINCHIP_WRITE( Sn_IR(s) , Sn_IR_SEND_OK);
#endif

   return ret;
}

uint16 send_TOP(SOCKET s, const uint8 * buf, uint16 len)
{
  uint8 status=0;
  uint16 ret=0;
  uint16 freesize=0;

  if (len > getIINCHIP_TxMAX(s)) ret = getIINCHIP_TxMAX(s); // check size not to exceed MAX size.
  else ret = len;

  // if freebuf is available, start.
  do
  {
    freesize = getSn_TX_FSR_TOP(s);
    status = IINCHIP_READ_TOP(Sn_SR(s));
    if ((status != SOCK_ESTABLISHED) && (status != SOCK_CLOSE_WAIT))
    {
      ret = 0;
      break;
    }
  } while (freesize < ret);
  
  // copy data
  send_data_processing_top(s, (uint8 *)buf, ret);
  IINCHIP_WRITE_TOP( Sn_CR(s) ,Sn_CR_SEND);

  /* wait to process the command... */
  while( IINCHIP_READ_TOP(Sn_CR(s) ) );

  while ( (IINCHIP_READ_TOP(Sn_IR(s) ) & Sn_IR_SEND_OK) != Sn_IR_SEND_OK )
  {
    status = IINCHIP_READ_TOP(Sn_SR(s));
    if ((status != SOCK_ESTABLISHED) && (status != SOCK_CLOSE_WAIT) )
    {
      close_TOP(s);
      return 0;
    }
  }
  IINCHIP_WRITE_TOP( Sn_IR(s) , Sn_IR_SEND_OK);

#ifdef __DEF_IINCHIP_INT__
   putISR(s, getISR(s) & (~Sn_IR_SEND_OK));
#else
   IINCHIP_WRITE_TOP( Sn_IR(s) , Sn_IR_SEND_OK);
#endif

   return ret;
}

/**
*@brief		This function is an application I/F function which is used to receive the data in TCP mode.
					It continues to wait for data as much as the application wants to receive.
*@param		s: socket number.
*@param		buf: data buffer to receive.
*@param		len: data length.
*@return  received data size for success else 0.
*/
uint16 recv(SOCKET s, uint8 * buf, uint16 len)
{
   uint16 ret=0;
   if ( len > 0 )
   {
      recv_data_processing(s, buf, len);
      IINCHIP_WRITE( Sn_CR(s) ,Sn_CR_RECV);
      /* wait to process the command... */
      while( IINCHIP_READ(Sn_CR(s) ));
      /* ------- */
      ret = len;
   }
   return ret;
}
uint16 recv_TOP(SOCKET s, uint8 * buf, uint16 len)
{
   uint16 ret=0;
   if ( len > 0 )
   {
      recv_data_processing_TOP(s, buf, len);
      IINCHIP_WRITE_TOP( Sn_CR(s) ,Sn_CR_RECV);
      /* wait to process the command... */
      while( IINCHIP_READ_TOP(Sn_CR(s) ));
      /* ------- */
      ret = len;
   }
   return ret;
}

/**
*@brief   This function is an application I/F function which is used to send the data for other then TCP mode.
					Unlike TCP transmission, The peer's destination address and the port is needed.
*@param		s: socket number.
*@param		buf: data buffer to send.
*@param		len: data length.
*@param		addr: IP address to send.
*@param		port: IP port to send.
*@return  This function return send data size for success else 0.
*/
uint16 sendto(SOCKET s, const uint8 * buf, uint16 len, uint8 * addr, uint16 port)
{
   uint16 ret=0;

   if (len > getIINCHIP_TxMAX(s)) 
   ret = getIINCHIP_TxMAX(s); // check size not to exceed MAX size.
   else ret = len;

   if( ((addr[0] == 0x00) && (addr[1] == 0x00) && (addr[2] == 0x00) && (addr[3] == 0x00)) || ((port == 0x00)) )//||(ret == 0) )
   {
      /* added return value */
      ret = 0;
   }
   else
   {
      IINCHIP_WRITE( Sn_DIPR0(s), addr[0]);
      IINCHIP_WRITE( Sn_DIPR1(s), addr[1]);
      IINCHIP_WRITE( Sn_DIPR2(s), addr[2]);
      IINCHIP_WRITE( Sn_DIPR3(s), addr[3]);
      IINCHIP_WRITE( Sn_DPORT0(s),(uint8)((port & 0xff00) >> 8));
      IINCHIP_WRITE( Sn_DPORT1(s),(uint8)(port & 0x00ff));
      // copy data
      send_data_processing(s, (uint8 *)buf, ret);
      IINCHIP_WRITE( Sn_CR(s) ,Sn_CR_SEND);
      /* wait to process the command... */
      while( IINCHIP_READ( Sn_CR(s) ) )
	  ;
      /* ------- */ 
     while( (IINCHIP_READ( Sn_IR(s) ) & Sn_IR_SEND_OK) != Sn_IR_SEND_OK )
     {
      if (IINCHIP_READ( Sn_IR(s) ) & Sn_IR_TIMEOUT)
      {
            /* clear interrupt */
      IINCHIP_WRITE( Sn_IR(s) , (Sn_IR_SEND_OK | Sn_IR_TIMEOUT)); /* clear SEND_OK & TIMEOUT */
      return 0;
      }
     }
      IINCHIP_WRITE( Sn_IR(s) , Sn_IR_SEND_OK);
   }
   return ret;
}
uint16 sendto_top(SOCKET s, const uint8 * buf, uint16 len, uint8 * addr, uint16 port)
{
   uint16 ret=0;

   if (len > getIINCHIP_TxMAX(s)) 
   ret = getIINCHIP_TxMAX(s); // check size not to exceed MAX size.
   else ret = len;

   if( ((addr[0] == 0x00) && (addr[1] == 0x00) && (addr[2] == 0x00) && (addr[3] == 0x00)) || ((port == 0x00)) )//||(ret == 0) )
   {
      /* added return value */
      ret = 0;
   }
   else
   {
      IINCHIP_WRITE_TOP( Sn_DIPR0(s), addr[0]);
      IINCHIP_WRITE_TOP( Sn_DIPR1(s), addr[1]);
      IINCHIP_WRITE_TOP( Sn_DIPR2(s), addr[2]);
      IINCHIP_WRITE_TOP( Sn_DIPR3(s), addr[3]);
      IINCHIP_WRITE_TOP( Sn_DPORT0(s),(uint8)((port & 0xff00) >> 8));
      IINCHIP_WRITE_TOP( Sn_DPORT1(s),(uint8)(port & 0x00ff));
      // copy data
      send_data_processing_top(s, (uint8 *)buf, ret);
      IINCHIP_WRITE_TOP( Sn_CR(s) ,Sn_CR_SEND);
      /* wait to process the command... */
      while( IINCHIP_READ_TOP( Sn_CR(s) ) )
	  ;
      /* ------- */ 
     while( (IINCHIP_READ_TOP( Sn_IR(s) ) & Sn_IR_SEND_OK) != Sn_IR_SEND_OK )
     {
      if (IINCHIP_READ_TOP( Sn_IR(s) ) & Sn_IR_TIMEOUT)
      {
            /* clear interrupt */
      IINCHIP_WRITE_TOP( Sn_IR(s) , (Sn_IR_SEND_OK | Sn_IR_TIMEOUT)); /* clear SEND_OK & TIMEOUT */
      return 0;
      }
     }
      IINCHIP_WRITE_TOP( Sn_IR(s) , Sn_IR_SEND_OK);
   }
   return ret;
}


/**
*@brief   This function is an application I/F function which is used to receive the data in other then
					TCP mode. This function is used to receive UDP, IP_RAW and MAC_RAW mode, and handle the header as well.
*@param		s: socket number.
*@param		buf: data buffer to receive.
*@param		len: data length.
*@param		addr: IP address to receive.
*@param		port: IP port to receive.
*@return	This function return received data size for success else 0.
*/
uint16 recvfrom(SOCKET s, uint8 * buf, uint16 len, uint8 * addr, uint16 *port) 
{
   uint8 head[8]={0,0,0,0,0,0,0,0};
   uint16 data_len=0;
   uint16 ptr=0;
   uint32 addrbsb =0;
   if ( len > 0 )
   {
        ptr     = IINCHIP_READ(Sn_RX_RD0(s) );                             /*  */
        ptr     = ((ptr & 0x00ff) << 8) + IINCHIP_READ(Sn_RX_RD1(s));      /*  */
        addrbsb = (uint32)(ptr<<8) +  (s<<5) + 0x18;
        
        switch (IINCHIP_READ(Sn_MR(s) ) & 0x07)
        {
            case Sn_MR_UDP :
                wiz_read_buf(addrbsb, head, 0x08);                 /* 向固定地址读取数据 */  
                ptr += 8;
                
                addr[0]  = head[0];																 /* 读取目标IP */
                addr[1]  = head[1];
                addr[2]  = head[2];
                addr[3]  = head[3];
                *port    = head[4];                                /* 读取目标端口号 */
                *port    = (*port << 8) + head[5];
                
                data_len = head[6];
                data_len = (data_len << 8) + head[7];              /* 读取数据长度 */
                
                addrbsb = (uint32)(ptr<<8) +  (s<<5) + 0x18;       /* 0X18代表选择socketn接受缓存 */                
            
            
                wiz_read_buf(addrbsb, buf, data_len);                
                ptr += data_len;
                IINCHIP_WRITE( Sn_RX_RD0(s), (uint8)((ptr & 0xff00) >> 8));
                IINCHIP_WRITE( Sn_RX_RD1(s), (uint8)(ptr & 0x00ff));
                break;
            default :
                break;
      }
      IINCHIP_WRITE( Sn_CR(s) ,Sn_CR_RECV);
      while( IINCHIP_READ( Sn_CR(s)) ) ;
   }
   return data_len;
}

uint16 recvfrom_top(SOCKET s, uint8 * buf, uint16 len, uint8 * addr, uint16 *port) 
{
    uint8 head[8]={0,0,0,0,0,0,0,0};
    uint16 data_len=0;
    uint16 ptr=0;
    uint32 addrbsb =0;
    if ( len > 0 )
    {
        ptr     = IINCHIP_READ_TOP(Sn_RX_RD0(s) );                             /*  */
        ptr     = ((ptr & 0x00ff) << 8) + IINCHIP_READ_TOP(Sn_RX_RD1(s));      /*  */
        addrbsb = (uint32)(ptr<<8) +  (s<<5) + 0x18;
        
        switch (IINCHIP_READ_TOP(Sn_MR(s) ) & 0x07)
        {
            case Sn_MR_UDP :
                wiz_read_buf_top(addrbsb, head, 0x08);                 /* 向固定地址读取数据 */  
                ptr += 8;
                
                addr[0]  = head[0];																 /* 读取目标IP */
                addr[1]  = head[1];
                addr[2]  = head[2];
                addr[3]  = head[3];
                *port    = head[4];                                /* 读取目标端口号 */
                *port    = (*port << 8) + head[5];
                
                data_len = head[6];
                data_len = (data_len << 8) + head[7];              /* 读取数据长度 */
                
                addrbsb = (uint32)(ptr<<8) +  (s<<5) + 0x18;       /* 0X18代表选择socketn接受缓存 */
                
                wiz_read_buf_top(addrbsb, buf, data_len);                
                ptr += data_len;
                IINCHIP_WRITE_TOP( Sn_RX_RD0(s), (uint8)((ptr & 0xff00) >> 8));
                IINCHIP_WRITE_TOP( Sn_RX_RD1(s), (uint8)(ptr & 0x00ff));
                break;
            default :
                break;
      }
      IINCHIP_WRITE_TOP( Sn_CR(s) ,Sn_CR_RECV);
      while( IINCHIP_READ_TOP( Sn_CR(s)) ) ;
   }
   return data_len;
}
#ifdef __MACRAW__
/**
*@brief   OPen the 0-th socket with MACRAW mode
*@param		None
*@return	None
*/
void macraw_open(void)
{
  uint8 sock_num=0;
  uint16 dummyPort = 0;
  uint8 mFlag = 0;
  sock_num = 0;
  close(sock_num); // Close the 0-th socket
  socket(sock_num, Sn_MR_MACRAW, dummyPort,mFlag); 
}

/**
*@brief   OPen the 0-th socket with MACRAW mode
*@param		buf: data buffer to send.
*@param		len: data length.
*@return	This function return sended data size for success else 0.
*/
uint16 macraw_send( const uint8 * buf, uint16 len )
{
   uint16 ret=0;
   uint8 sock_num;
   sock_num =0;


   if (len > getIINCHIP_TxMAX(sock_num)) ret = getIINCHIP_TxMAX(sock_num); // check size not to exceed MAX size.
   else ret = len;

   send_data_processing(sock_num, (uint8 *)buf, len);

   //W5500 SEND COMMAND
   IINCHIP_WRITE(Sn_CR(sock_num),Sn_CR_SEND);
   while( IINCHIP_READ(Sn_CR(sock_num)) );
   while ( (IINCHIP_READ(Sn_IR(sock_num)) & Sn_IR_SEND_OK) != Sn_IR_SEND_OK );
   IINCHIP_WRITE(Sn_IR(sock_num), Sn_IR_SEND_OK);

   return ret;
}

/**
*@brief   OPen the 0-th socket with MACRAW mode
*@param		buf: data buffer to send.
*@param		len: data length.
*@return	This function return received data size for success else 0.
*/
uint16 macraw_recv( uint8 * buf, uint16 len )
{
   uint8 sock_num;
   uint16 data_len=0;
   uint16 dummyPort = 0;
   uint16 ptr = 0;
   uint8 mFlag = 0;
   sock_num = 0;

   if ( len > 0 )
   {

      data_len = 0;

      ptr = IINCHIP_READ(Sn_RX_RD0(sock_num));
      ptr = (uint16)((ptr & 0x00ff) << 8) + IINCHIP_READ( Sn_RX_RD1(sock_num) );
      //-- read_data(s, (uint8 *)ptr, data, len); // read data
      data_len = IINCHIP_READ_RXBUF(0, ptr);
      ptr++;
      data_len = ((data_len<<8) + IINCHIP_READ_RXBUF(0, ptr)) - 2;
      ptr++;

      if(data_len > 1514)
      {
         /** recommand : close and open **/
         close(sock_num); // Close the 0-th socket
         socket(sock_num, Sn_MR_MACRAW, dummyPort,mFlag);  // OPen the 0-th socket with MACRAW mode
         return 0;
      }

      IINCHIP_READ_RXBUF_BURST(sock_num, ptr, data_len, (uint8*)(buf));
      ptr += data_len;

      IINCHIP_WRITE(Sn_RX_RD0(sock_num),(uint8)((ptr & 0xff00) >> 8));
      IINCHIP_WRITE(Sn_RX_RD1(sock_num),(uint8)(ptr & 0x00ff));
      IINCHIP_WRITE(Sn_CR(sock_num), Sn_CR_RECV);
      while( IINCHIP_READ(Sn_CR(sock_num)) ) ;
   }

   return data_len;
}
#endif
