YangXiao69/WSPS-325-150K-PEFA/Software/WSPS-325-150K-PEFA-291-V1.0/User/bsp/bsp_spi/bsp_spi.c

#include "main.h"




SPI_HandleTypeDef hspi2;

/* SPI1 init function */
void SPI2_Init(void)
{

  hspi2.Instance = SPI2;
  hspi2.Init.Mode = SPI_MODE_MASTER;
  hspi2.Init.Direction = SPI_DIRECTION_2LINES;
  hspi2.Init.DataSize = SPI_DATASIZE_8BIT;
  hspi2.Init.CLKPolarity = SPI_POLARITY_HIGH;
  hspi2.Init.CLKPhase = SPI_PHASE_2EDGE;
  hspi2.Init.NSS = SPI_NSS_SOFT;
  hspi2.Init.BaudRatePrescaler = SPI_BAUDRATEPRESCALER_8;
  hspi2.Init.FirstBit = SPI_FIRSTBIT_MSB;
  hspi2.Init.TIMode = SPI_TIMODE_DISABLE;
  hspi2.Init.CRCCalculation = SPI_CRCCALCULATION_DISABLE;
  hspi2.Init.CRCPolynomial = 7;
  hspi2.Init.CRCLength = SPI_CRC_LENGTH_DATASIZE;
  hspi2.Init.NSSPMode = SPI_NSS_PULSE_ENABLE;
  if (HAL_SPI_Init(&hspi2) != HAL_OK)
  {
    Error_Handler();
  }
  
  
   __HAL_SPI_ENABLE(&hspi2); 

}

void HAL_SPI_MspInit(SPI_HandleTypeDef* spiHandle)
{

  GPIO_InitTypeDef GPIO_InitStruct = {0};
  if(spiHandle->Instance==SPI2)
  {
    /* SPI2 clock enable */
    __HAL_RCC_SPI2_CLK_ENABLE();
  
    __HAL_RCC_GPIOB_CLK_ENABLE();
    __HAL_RCC_GPIOC_CLK_ENABLE();
    /**SPI2 GPIO Configuration    
    PB13     ------> SPI2_SCK
    PB14     ------> SPI2_MISO
    PB15     ------> SPI2_MOSI 
    */
    GPIO_InitStruct.Pin = GPIO_PIN_13 | GPIO_PIN_14 | GPIO_PIN_15;
    GPIO_InitStruct.Mode = GPIO_MODE_AF_PP;
    GPIO_InitStruct.Pull = GPIO_NOPULL;
    GPIO_InitStruct.Speed = GPIO_SPEED_FREQ_VERY_HIGH;
    GPIO_InitStruct.Alternate = GPIO_AF5_SPI2;
    HAL_GPIO_Init(GPIOB, &GPIO_InitStruct);
      
      
    GPIO_InitStruct.Pin = GPIO_PIN_12;
    GPIO_InitStruct.Mode = GPIO_MODE_OUTPUT_PP;
    GPIO_InitStruct.Pull = GPIO_PULLUP;
    GPIO_InitStruct.Speed = GPIO_SPEED_FREQ_VERY_HIGH;
    HAL_GPIO_Init(GPIOB, &GPIO_InitStruct);   
      
    GPIO_InitStruct.Pin = GPIO_PIN_7;
    GPIO_InitStruct.Mode = GPIO_MODE_OUTPUT_PP;
    GPIO_InitStruct.Pull = GPIO_PULLUP;
    GPIO_InitStruct.Speed = GPIO_SPEED_FREQ_VERY_HIGH;
    HAL_GPIO_Init(GPIOC, &GPIO_InitStruct);        

  }
}

void HAL_SPI_MspDeInit(SPI_HandleTypeDef* spiHandle)
{

  if(spiHandle->Instance==SPI2)
  {
    /* Peripheral clock disable */
    __HAL_RCC_SPI2_CLK_DISABLE();
  
    /**SPI1 GPIO Configuration    
    PA5     ------> SPI1_SCK
    PA6     ------> SPI1_MISO
    PA7     ------> SPI1_MOSI 
    */
    HAL_GPIO_DeInit(GPIOB, GPIO_PIN_13 | GPIO_PIN_14 | GPIO_PIN_15);

  }
} 

/* USER CODE BEGIN 1 */


/** 
	*	SPI速度设置函数
  * SPI速度=fAPB1/分频系数
  * @ref SPI_BaudRate_Prescaler:SPI_BAUDRATEPRESCALER_2~SPI_BAUDRATEPRESCALER_2 256
  * fAPB1时钟一般为42Mhz：
	*/
void SPI2_SetSpeed(uint8_t SPI_BaudRatePrescaler)
{
    assert_param(IS_SPI_BAUDRATE_PRESCALER(SPI_BaudRatePrescaler));//判断有效性
    __HAL_SPI_DISABLE(&hspi2);            //关闭SPI
    hspi2.Instance->CR1&=0XFFC7;          //位3-5清零，用来设置波特率
    hspi2.Instance->CR1|=SPI_BaudRatePrescaler;//设置SPI速度
    __HAL_SPI_ENABLE(&hspi2);             //使能SPI
    
}


/**
  * 函数功能: 往串行Flash读取写入一个字节数据并接收一个字节数据
  * 输入参数: byte：待发送数据
  * 返 回 值: uint8_t：接收到的数据
  * 说    明：无
  */
uint8_t SPIx_ReadWriteByte(SPI_HandleTypeDef* hspi,uint8_t byte)
{
  uint8_t d_read,d_send=byte;
  if(HAL_SPI_TransmitReceive(hspi,&d_send,&d_read,1,0xFF)!=HAL_OK)
  {
    d_read=0xFF;
  }
  return d_read; 
}



uint8_t SPI2_SendByte(uint8_t byte)
{
	uint8_t status = 0;
	uint8_t SPI2TxBuf[1] = {0};
	uint8_t SPI2RxBuf[1] = {0};	
	
	uint8_t retval = 0;
	
	SPI2TxBuf[0] = byte;
	
	status = HAL_SPI_TransmitReceive(&hspi2, (uint8_t*)SPI2TxBuf, (uint8_t *)SPI2RxBuf, 1, 1000000);
	
	if( status!= HAL_OK)	
	{
		_Error_Handler(__FILE__, __LINE__);
	}
	
	retval = SPI2RxBuf[0];
	
	return retval;
}
