YangXiao69/WSPS-325-150K-PEFA/Software/WSPS-325-150K-PEFA-438-1-V1.0/Core/Src/usart.c

/**
  ******************************************************************************
  * @file    usart.c
  * @brief   This file provides code for the configuration
  *          of the USART instances.
  ******************************************************************************
  * @attention
  *
  * <h2><center>&copy; Copyright (c) 2022 STMicroelectronics.
  * All rights reserved.</center></h2>
  *
  * This software component is licensed by ST under BSD 3-Clause license,
  * the "License"; You may not use this file except in compliance with the
  * License. You may obtain a copy of the License at:
  *                        opensource.org/licenses/BSD-3-Clause
  *
  ******************************************************************************
  */

/* Includes ------------------------------------------------------------------*/
#include "usart.h"

/* USER CODE BEGIN 0 */
#include "../../App/dc_rs485.h"
/* USER CODE END 0 */

UART_HandleTypeDef huart3;
DMA_HandleTypeDef hdma_usart3_rx;
DMA_HandleTypeDef hdma_usart3_tx;

/* USART3 init function */

void MX_USART3_UART_Init(void)
{

  huart3.Instance = USART3;
  huart3.Init.BaudRate = 9600;
  huart3.Init.WordLength = UART_WORDLENGTH_8B;
  huart3.Init.StopBits = UART_STOPBITS_1;
  huart3.Init.Parity = UART_PARITY_NONE;
  huart3.Init.Mode = UART_MODE_TX_RX;
  huart3.Init.HwFlowCtl = UART_HWCONTROL_NONE;
  huart3.Init.OverSampling = UART_OVERSAMPLING_8;
  huart3.Init.OneBitSampling = UART_ONE_BIT_SAMPLE_DISABLE;
  huart3.Init.ClockPrescaler = UART_PRESCALER_DIV1;
  huart3.AdvancedInit.AdvFeatureInit = UART_ADVFEATURE_RXOVERRUNDISABLE_INIT|UART_ADVFEATURE_DMADISABLEONERROR_INIT;
  huart3.AdvancedInit.OverrunDisable = UART_ADVFEATURE_OVERRUN_DISABLE;
  huart3.AdvancedInit.DMADisableonRxError = UART_ADVFEATURE_DMA_DISABLEONRXERROR;
  if (HAL_UART_Init(&huart3) != HAL_OK)
  {
    Error_Handler();
  }
  if (HAL_UARTEx_SetTxFifoThreshold(&huart3, UART_TXFIFO_THRESHOLD_1_8) != HAL_OK)
  {
    Error_Handler();
  }
  if (HAL_UARTEx_SetRxFifoThreshold(&huart3, UART_RXFIFO_THRESHOLD_1_8) != HAL_OK)
  {
    Error_Handler();
  }
  if (HAL_UARTEx_DisableFifoMode(&huart3) != HAL_OK)
  {
    Error_Handler();
  }
}

void HAL_UART_MspInit(UART_HandleTypeDef* uartHandle)
{

  GPIO_InitTypeDef GPIO_InitStruct = {0};
  RCC_PeriphCLKInitTypeDef PeriphClkInitStruct = {0};
  if(uartHandle->Instance==USART3)
  {
  /** Initializes the peripherals clock
  */
    PeriphClkInitStruct.PeriphClockSelection = RCC_PERIPHCLK_USART3;
    PeriphClkInitStruct.Usart234578ClockSelection = RCC_USART234578CLKSOURCE_D2PCLK1;
    if (HAL_RCCEx_PeriphCLKConfig(&PeriphClkInitStruct) != HAL_OK)
    {
      Error_Handler();
    }

    /* USART3 clock enable */
    __HAL_RCC_USART3_CLK_ENABLE();

    __HAL_RCC_GPIOD_CLK_ENABLE();
    /**USART3 GPIO Configuration
    PD8     ------> USART3_TX
    PD9     ------> USART3_RX
    */
    GPIO_InitStruct.Pin = GPIO_PIN_8|GPIO_PIN_9;
    GPIO_InitStruct.Mode = GPIO_MODE_AF_PP;
    GPIO_InitStruct.Pull = GPIO_NOPULL;
    GPIO_InitStruct.Speed = GPIO_SPEED_FREQ_LOW;
    GPIO_InitStruct.Alternate = GPIO_AF7_USART3;
    HAL_GPIO_Init(GPIOD, &GPIO_InitStruct);

    /* USART3 DMA Init */
    /* USART3_RX Init */
    hdma_usart3_rx.Instance = DMA1_Stream0;
    hdma_usart3_rx.Init.Request = DMA_REQUEST_USART3_RX;
    hdma_usart3_rx.Init.Direction = DMA_PERIPH_TO_MEMORY;
    hdma_usart3_rx.Init.PeriphInc = DMA_PINC_DISABLE;
    hdma_usart3_rx.Init.MemInc = DMA_MINC_ENABLE;
    hdma_usart3_rx.Init.PeriphDataAlignment = DMA_PDATAALIGN_BYTE;
    hdma_usart3_rx.Init.MemDataAlignment = DMA_MDATAALIGN_BYTE;
    hdma_usart3_rx.Init.Mode = DMA_NORMAL;
    hdma_usart3_rx.Init.Priority = DMA_PRIORITY_LOW;
    hdma_usart3_rx.Init.FIFOMode = DMA_FIFOMODE_DISABLE;
    if (HAL_DMA_Init(&hdma_usart3_rx) != HAL_OK)
    {
      Error_Handler();
    }

    __HAL_LINKDMA(uartHandle,hdmarx,hdma_usart3_rx);

    /* USART3_TX Init */
    hdma_usart3_tx.Instance = DMA1_Stream1;
    hdma_usart3_tx.Init.Request = DMA_REQUEST_USART3_TX;
    hdma_usart3_tx.Init.Direction = DMA_MEMORY_TO_PERIPH;
    hdma_usart3_tx.Init.PeriphInc = DMA_PINC_DISABLE;
    hdma_usart3_tx.Init.MemInc = DMA_MINC_ENABLE;
    hdma_usart3_tx.Init.PeriphDataAlignment = DMA_PDATAALIGN_BYTE;
    hdma_usart3_tx.Init.MemDataAlignment = DMA_MDATAALIGN_BYTE;
    hdma_usart3_tx.Init.Mode = DMA_NORMAL;
    hdma_usart3_tx.Init.Priority = DMA_PRIORITY_LOW;
    hdma_usart3_tx.Init.FIFOMode = DMA_FIFOMODE_DISABLE;
    if (HAL_DMA_Init(&hdma_usart3_tx) != HAL_OK)
    {
      Error_Handler();
    }

    __HAL_LINKDMA(uartHandle,hdmatx,hdma_usart3_tx);

    /* USART3 interrupt Init */
    HAL_NVIC_SetPriority(USART3_IRQn, 0, 0);
    HAL_NVIC_EnableIRQ(USART3_IRQn);
  /* USER CODE BEGIN USART3_MspInit 1 */
    __HAL_UART_ENABLE_IT(&huart3,UART_IT_IDLE);
    HAL_UART_Receive_DMA(&huart3,UART3_DMA_RX,64);

  /* USER CODE END USART3_MspInit 1 */
  }
}

void HAL_UART_MspDeInit(UART_HandleTypeDef* uartHandle)
{

  if(uartHandle->Instance==USART3)
  {
    /* Peripheral clock disable */
    __HAL_RCC_USART3_CLK_DISABLE();

    /**USART3 GPIO Configuration
    PD8     ------> USART3_TX
    PD9     ------> USART3_RX
    */
    HAL_GPIO_DeInit(GPIOD, GPIO_PIN_8|GPIO_PIN_9);

    /* USART3 DMA DeInit */
    HAL_DMA_DeInit(uartHandle->hdmarx);
    HAL_DMA_DeInit(uartHandle->hdmatx);

    /* USART3 interrupt Deinit */
    HAL_NVIC_DisableIRQ(USART3_IRQn);
  }
}

/* USER CODE BEGIN 1 */

void HAL_UART_RxCpltCallback(UART_HandleTypeDef* uartHandle)
{
    uint32_t temp = 0;

    

}

void HAL_UART_IDLECallback(UART_HandleTypeDef* uartHandle)
{
    uint32_t temp = 0;
    
    if(USART3 == uartHandle->Instance)
    {
        if(__HAL_UART_GET_FLAG(&huart3, UART_FLAG_IDLE) != RESET) //如果产生串口空闲中断
        {		
            __HAL_UART_CLEAR_IDLEFLAG(&huart3);          	//这句话很关键，没有这句话无法清除串口空闲中断	
            HAL_UART_DMAStop(&huart3); 
            DC_Power_Reivce();
            temp  =  __HAL_DMA_GET_COUNTER(&hdma_usart3_rx);// 获取DMA中未传输的数据个数 
            HAL_UART_Receive_DMA(&huart3, UART3_DMA_RX, 64);
        }    
    }


}


void HAL_UART_TxCpltCallback(UART_HandleTypeDef* uartHandle)
{

    __HAL_UART_CLEAR_IDLEFLAG(uartHandle);

}


/* USER CODE END 1 */

/************************ (C) COPYRIGHT STMicroelectronics *****END OF FILE****/
