YangXiao69/WSPS-325-150K-PEFA/Software/WSPS-325-150K-PEFA-438-3-V1.0/App/task.c

#include "task.h"
#include "../../W5500/w5500_conf.h"
#include "../../App/led.h"
#include "bsp_i2c_ee.h"
#include "ds18b20.h"


uint16_t Modbus[1024];
struct sSystem System;

struct sAmplifierModule AmplifierModule[48];
struct sDC_Power DC_Power[12];
struct sSlave_Device Slave_Device[4];

//延时nus
// nus为要延时的us数.
void delay_us(uint32_t nus)
{
    uint32_t temp = 0;
    if (nus > 39000)
    {
        nus = 39000;
    }

    SysTick->LOAD = nus * 480;                //时间加载
    SysTick->VAL = 0x00;                      //清空计数器
    SysTick->CTRL |= SysTick_CTRL_ENABLE_Msk; //开始倒数
    do
    {
        temp = SysTick->CTRL;
    } while ((temp & 0x01) && !(temp & (1 << 16))); //等待时间到达

    SysTick->CTRL &= ~SysTick_CTRL_ENABLE_Msk; //关闭计数器
    SysTick->VAL = 0x00;                       //清空计数器
}

//延时nms
//注意nms的范围
// SysTick->LOAD为24位寄存器,所以,最大延时为:
// nms<=0xffffff*8*1000/SYSCLK
// SYSCLK单位为Hz,nms单位为ms
//对72M条件下,nms<=1864
void delay_ms(uint16_t nms)
{
  uint32_t temp = 0;
  if (nms > 39)
  {
    nms = 39;
  }

  SysTick->LOAD = (uint32_t)nms * 48000;    //时间加载(SysTick->LOAD为24bit)
  SysTick->VAL = 0x00;                      //清空计数器
  SysTick->CTRL |= SysTick_CTRL_ENABLE_Msk; //开始倒数
  do
  {
    temp = SysTick->CTRL;
  } while ((temp & 0x01) && !(temp & (1 << 16))); //等待时间到达
  SysTick->CTRL &= ~SysTick_CTRL_ENABLE_Msk;      //关闭计数器
  SysTick->VAL = 0x00;                            //清空计数器
}




void Device_Init(void)
{
    I2C_EE_Init();
    
    w5500_init();       /*spi4  udp*/
    socket_buf_init(txsize, rxsize); /*初始化8个Socket的发送接收缓存大小*/

    w5500_top_init();   /*spi2   tcp*/
    socket_buf_init_top(txsize, rxsize); /*初始化8个Socket的发送接收缓存大小*/
    
}

void Ptt_Control(uint8_t sw)
{
    if(sw == ON)
    {
        HAL_GPIO_WritePin(GPIOE,GPIO_PIN_0,GPIO_PIN_SET);
        HAL_GPIO_WritePin(GPIOF,GPIO_PIN_11,GPIO_PIN_SET);        
    }
    else
    {
        HAL_GPIO_WritePin(GPIOE,GPIO_PIN_0,GPIO_PIN_RESET);
        HAL_GPIO_WritePin(GPIOF,GPIO_PIN_11,GPIO_PIN_RESET); 
    }

}

void DC_Power_Control(uint8_t sw)           /*一起控还是分开控*/
{
    if(sw == ON)
    {
        HAL_GPIO_WritePin(GPIOF,GPIO_PIN_4,GPIO_PIN_SET);       
    }
    else
    {
        HAL_GPIO_WritePin(GPIOF,GPIO_PIN_4,GPIO_PIN_RESET); 
        System.RF = 0; 
        System.Pset = 0;
    }
    
    LED_DC_Power(sw);
}

void Task_Control(void)
{
    DC_Power_Control(System.Power);
    Ptt_Control(System.RF);
}

void Task_Write_Modbus(void)
{
    static uint8_t i = 0 ,pA = 0,sd;
    uint8_t Addr;
    
    Modbus[0x0011] = System.Modbus_Addr;
    
    Modbus[0x0080] = System.Power;                  /* 电源 */
    Modbus[0x0081] = System.RF ;                      /* 射频 */
    Modbus[0x0082] = System.Pset ;                 

    Modbus[0x0086] = System.Duty;
    Modbus[0x0087] = System.PulseWidth;


    Modbus[0x00A1] = System.PowerOut;
    Modbus[0x00A2] = System.PowerR;
    Modbus[0x00A3] = System.PowerZB;
    Modbus[0x00A4] = System.PfoutOut;  


//    Modbus[0x00AF] = System.Temp.PCB_Borad;
      
    Addr = sd*0x03;
    Modbus[0x00f0 + Addr] = System.Pout_factor[System.Mode];
    Modbus[0x00f1 + Addr] = System.PRout_factor;
    Modbus[0x00f2 + Addr] = System.fPout_factor;
    sd++;
    if(sd >= 4)     /*4个从机控制盒*/
        sd = 0;    
    
    Addr = i * 0x0a;
    Modbus[0x0100 + Addr] = AmplifierModule[i].Addr;   //
    Modbus[0x0101 + Addr] = AmplifierModule[i].Powerout; // 
    Modbus[0x0102 + Addr] = AmplifierModule[i].PowerR; // 
    Modbus[0x0103 + Addr] = AmplifierModule[i].Voltage; // 
    Modbus[0x0104 + Addr] = AmplifierModule[i].Current[0]; //电流
    Modbus[0x0105 + Addr] = AmplifierModule[i].Current[1]; //电流
    Modbus[0x0106 + Addr] = AmplifierModule[i].Current[2]; //电流
    Modbus[0x0107 + Addr] = AmplifierModule[i].Current[3]; //电流
    Modbus[0x0108 + Addr] = AmplifierModule[i].Temp; //
    Modbus[0x0109 + Addr] = AmplifierModule[i].error; //
    i++;
    if(i >= 48)     /*48个功放插件*/
        i = 0;
    
    Addr = pA * 0x03;
    Modbus[0x370 + Addr] = DC_Power[pA].Voltage;
    Modbus[0x371 + Addr] = DC_Power[pA].Current; 
    Modbus[0x372 + Addr] = DC_Power[pA].Temp;
    pA++;
    if(pA >= 12)        /*12个电源插件*/
        pA = 0;
}


void Task_Ads8411_Receive_Data(void)
{
    if(HAL_GPIO_ReadPin(S_CLK_GPIO_Port, S_CLK_Pin))
    {
        System.PowerOut= GPIOG->IDR;
    }
    else
    {
        System.PowerR = GPIOG->IDR;
    }

}

void Task_Get_temp(void)
{
   System.Temp = DS18B20_Get_Temp(1);

}
