YangXiao69/WSPS-325-150K-PEFA/Software/WSPS-325-150K-PEFA-438-2-V1.0/App/ads8411.c

#include "ads8411.h"


/*
   adsBUSY    PE6   读取状态为 1 时 表示正在进行转换
	 adsRESET   PE5   复位低电平有效
	 adsBYTE    PE4   设置 1 时 读取数据从0-15位？
	 adsCONVST  PE3   开始转换 低电平有效
	 adsCS      PB5   片选 低电平有效
	 adsRD      PE2   同步输出，读取为 0 时，表示总线输出可读取

	 使用方式：adsCS始终拉低，adsRD作为读取使用 adsBYTE默认为0，adsBYTE为1时，再次读取15：8为7：0的数据（在引脚不够用的情况下使用，本次使用）

	 Timing for Conversion and Acquisition Cycles With CS Tied to BDGND, RD Toggling
*/



void adsCONVST_Start_A(void)
{
    while(HAL_GPIO_ReadPin(AD1_BUSY_GPIO_Port,AD1_BUSY_Pin));    //等待 adsBUSY 信号消失
    HAL_GPIO_WritePin(AD1_CS_GPIO_Port,AD1_CS_Pin,GPIO_PIN_RESET);  //adsCS = 0;
    HAL_GPIO_WritePin(AD1_BYTE_GPIO_Port,AD1_BYTE_Pin,GPIO_PIN_RESET);  //adsBYTE = 0;
    HAL_GPIO_WritePin(AD1_RD_GPIO_Port,AD1_RD_Pin,GPIO_PIN_RESET);  //adsRD = 0;
    HAL_GPIO_WritePin(AD1_CONVST_GPIO_Port,AD1_CONVST_Pin,GPIO_PIN_SET);   /*CONVST = 1*/
    delay_10ns(50);
    HAL_GPIO_WritePin(AD1_CONVST_GPIO_Port,AD1_CONVST_Pin,GPIO_PIN_RESET);   /*CONVST = 0*/
    while(HAL_GPIO_ReadPin(AD1_BUSY_GPIO_Port,AD1_BUSY_Pin));    //等待 adsBUSY 信号消失
}

void ads8411_reset_A(void)
{
    HAL_GPIO_WritePin(AD1_CS_GPIO_Port,AD1_CS_Pin,GPIO_PIN_RESET);  //adsCS = 0;
    HAL_GPIO_WritePin(AD1_RESET_GPIO_Port,AD1_RESET_Pin,GPIO_PIN_RESET);  //adsRESET = 0;
    delay_ms(10);
    HAL_GPIO_WritePin(AD1_RESET_GPIO_Port,AD1_RESET_Pin,GPIO_PIN_SET);    //adsRESET = 1;
}

uint16_t ads8411_Conversion_A(void)
{
    uint16_t data;
    adsCONVST_Start_A();

    delay_10ns(50);
    data = ((uint16_t)GPIOD->IDR);
    return data;
}

uint16_t get_ADS8411Data_A(void)
{
    uint16_t i=0, data=0;
    uint16_t MaxData=0;

    for(i=0; i<1000; i++)    // 1ms
    {
        data = ads8411_Conversion_A();
        if(MaxData < data)	
            MaxData = data;
    }
    return MaxData;
}

/***********************************************************************/

void adsCONVST_Start_B(void)
{
    while(HAL_GPIO_ReadPin(AD2_BUSY_GPIO_Port,AD2_BUSY_Pin));    //等待 adsBUSY 信号消失
    HAL_GPIO_WritePin(AD2_CS_GPIO_Port,AD2_CS_Pin,GPIO_PIN_RESET);  //adsCS = 0;
    HAL_GPIO_WritePin(AD2_BYTE_GPIO_Port,AD2_BYTE_Pin,GPIO_PIN_RESET);  //adsBYTE = 0;
    HAL_GPIO_WritePin(AD2_RD_GPIO_Port,AD2_RD_Pin,GPIO_PIN_RESET);  //adsRD = 0;
    HAL_GPIO_WritePin(AD2_CONVST_GPIO_Port,AD2_CONVST_Pin,GPIO_PIN_SET);   /*CONVST = 1*/
    delay_10ns(50);
    HAL_GPIO_WritePin(AD2_CONVST_GPIO_Port,AD2_CONVST_Pin,GPIO_PIN_RESET);   /*CONVST = 0*/
    while(HAL_GPIO_ReadPin(AD2_BUSY_GPIO_Port,AD2_BUSY_Pin));    //等待 adsBUSY 信号消失
}

void ads8411_reset_B(void)
{
    HAL_GPIO_WritePin(AD2_CS_GPIO_Port,AD2_CS_Pin,GPIO_PIN_RESET);  //adsCS = 0;
    HAL_GPIO_WritePin(AD2_RESET_GPIO_Port,AD2_RESET_Pin,GPIO_PIN_RESET);  //adsRESET = 0;
    delay_ms(10);
    HAL_GPIO_WritePin(AD2_RESET_GPIO_Port,AD2_RESET_Pin,GPIO_PIN_SET);    //adsRESET = 1;
}

uint16_t ads8411_Conversion_B(void)
{
    uint16_t data;
    adsCONVST_Start_B();

    delay_10ns(50);
    data = ((uint16_t)GPIOE->IDR);
    return data;
}

uint16_t get_ADS8411Data_B(void)
{
    uint16_t i=0, data=0;
    uint16_t MaxData=0;

    for(i=0; i<1000; i++)    // 1ms
    {
        data = ads8411_Conversion_B();
        if(MaxData < data)	
            MaxData = data;
    }
    return MaxData;
}
