YangXiao69/WSPS-325-150K-PEFA/Software/WSPS-325-150K-PEFA-438-1-V1.0/App/dc_rs485.c

#include "dc_rs485.h"
#include "task.h"
#include "usart.h"

uint8_t UART3_DMA_TX[64];
uint8_t UART3_DMA_RX[64];

/*
 *  CRC校验
 */
uint16_t crc16_modbus(uint8_t *data, uint8_t length) // 0106000100179804
{
    uint8_t i = 0;
    uint16_t crc = 0xffff; // Initial value
    while (length--)
    {
        crc ^= *data++; // crc ^= *data; data++;
        for (i = 0; i < 8; ++i)
        {
            if (crc & 1)
                crc = (crc >> 1) ^ 0xA001; // 0xA001 = reverse 0x8005
            else
                crc = (crc >> 1);
        }
    }
    return crc;
}

void USART3_Send(uint8_t len)
{
	HAL_UART_Transmit_DMA(&huart3, UART3_DMA_TX, len); 
}


void Task_DC_Read_Data(void)
{
    uint16_t CRCNum;
    static uint8_t PowerAddr;
    static uint16_t i = 0;
    if(i >= 1000)
    {
        i = 0;
        if (PowerAddr >= 4)     /*3个电源插件*/
        {
            PowerAddr = 1;
        }
        UART3_DMA_TX[0] = PowerAddr;
        UART3_DMA_TX[1] = 0x03;
        UART3_DMA_TX[2] = 0x00;
        UART3_DMA_TX[3] = 0x00;
        UART3_DMA_TX[4] = 0x00;
        UART3_DMA_TX[5] = 0x07; 
        CRCNum = crc16_modbus((uint8_t *)UART3_DMA_TX, 6);
        UART3_DMA_TX[6] = CRCNum;
        UART3_DMA_TX[7] = CRCNum >> 8;
        USART3_Send(8);
        
        PowerAddr++;
    }
    i++;
}


void DC_Power_Reivce(void)
{
    if(UART3_DMA_RX[0] <= 3)
    {
        DC_Power[UART3_DMA_RX[0]-1].Voltage= (uint16_t)(UART3_DMA_RX[7] << 8)+UART3_DMA_RX[8];
        DC_Power[UART3_DMA_RX[0]-1].Current= (uint16_t)(UART3_DMA_RX[5] << 8)+UART3_DMA_RX[6];
        DC_Power[UART3_DMA_RX[0]-1].Temp= (uint16_t)(UART3_DMA_RX[15] << 8)+UART3_DMA_RX[16];
    }
}
