YangXiao69/WSPS-325-150K-PEFA/Software/WSPS-325-150K-PEFA-431-V1.0/User/bsp/bsp_gpio.h

#ifndef __BSP_GPIO_H
#define __BSP_GPIO_H

#include "stm32f10x.h"

void PPT_SW_init(void);
void LED_Init(void);

void LED_OFF(uint16_t name);
void LED_ON(uint16_t name);

#define ON 1
#define OFF 0



#endif 
