YangXiao69/WSPS-325-150K-PEFA/Software/WSPS-325-150K-PEFA-431-V1.0/User/bsp/bsp_ds18b20.h

#ifndef __BSP_DS18B20_H
#define __BSP_DS18B20_H

#include "stm32f10x.h"


/*引脚定义*/
/************************************************************/

#define DS18B20_PIN GPIO_Pin_3
#define DS18B20_PORT GPIOD
#define DS18B20_CLK_ENABLE() __GPIOD_CLK_ENABLE()

/************************************************************/

void DS18B20_GPIO_Config(void);

#endif



/*********************************************END OF FILE*************************************/
