YangXiao69/WSPS-325-150K-PEFA/测试/WSPS-325-150K-CEWG-292-V1.0-test/User/bsp/bsp_adf4351/bsp_adf4351.c

#include "system.h" 


unsigned long int N1_Cdata[1001] ={0x4B0000,  //2400
0x4B0008,
0x4B0008,
0x4B0018,
0x4B0008,
0x4B0008,			  
0x4B0018,
0x4B0038,
0x4B0008,
0x4B0048,
0x4B0008,
0x4B0058,
0x4B0018,
0x4B0068,
0x4B0038,
0x4B0018,
0x4B0008,
0x4B0088,
0x4B0048,
0x4B0098,
0x4B0008,
0x4B00A8,
0x4B0058,
0x4B00B8,
0x4B0018,
0x4B0028,
0x4B0068,
0x4B00D8,
0x4B0038,
0x4B00E8,
0x4B0018,
0x4B00F8,
0x4B0008,
0x4B0108,
0x4B0088,
0x4B0038,
0x4B0048,
0x4B0128,
0x4B0098,
0x4B0138,
0x4B0008,
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
};      








unsigned long int N2_Cdata[1001] ={0x8008009,  //2400        
0x8008501,        
0x8008281,        
0x8008501,        
0x8008141,        
0x8008101,        
0x8008281,        
0x8008501,        
0x80080A1,        
0x8008501,        
0x8008081,       
0x8008501,        
0x8008141,        
0x8008501,        
0x8008281,       
0x8008101,        
0x8008051,        
0x8008501,        
0x8008281,        
0x8008501,        
0x8008041,        
0x8008501,        
0x8008281,        
0x8008501,        
0x80080A1,        
0x8008101,        
0x8008281,        
0x8008501,        
0x8008141,        
0x8008501,        
0x8008081,        
0x8008501,        
0x8008029,        
0x8008501,        
0x8008281,        
0x8008101,       
0x8008141,        
0x8008501,        
0x8008281,        
0x8008501,        
0x8008021,        
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
};


uint16_t PLL_CLK  = GPIO_Pin_10;
uint16_t PLL_NSS  = GPIO_Pin_0 ;
uint16_t PLL_DATA = GPIO_Pin_12;
uint16_t PLL_LE   = GPIO_Pin_11;


void ADF4351_GPIO_Init(void)
{    
    GPIO_InitTypeDef GPIO_InitStructure                 ;                                                                                            
    RCC_AHB1PeriphClockCmd(RCC_AHB1Periph_GPIOC, ENABLE);   
    RCC_AHB1PeriphClockCmd(RCC_AHB1Periph_GPIOD, ENABLE); 
    
    GPIO_InitStructure.GPIO_Pin   = GPIO_Pin_10 | GPIO_Pin_11| GPIO_Pin_12;	
    GPIO_InitStructure.GPIO_Mode  = GPIO_Mode_OUT   ;    
    GPIO_InitStructure.GPIO_OType = GPIO_OType_PP   ;
    GPIO_InitStructure.GPIO_PuPd  = GPIO_PuPd_UP    ;
    GPIO_InitStructure.GPIO_Speed = GPIO_Speed_25MHz;                         
    GPIO_Init(GPIOC, &GPIO_InitStructure)           ;  
    
    GPIO_InitStructure.GPIO_Pin   = GPIO_Pin_0      ;	
    GPIO_InitStructure.GPIO_Mode  = GPIO_Mode_OUT   ;    
    GPIO_InitStructure.GPIO_OType = GPIO_OType_PP   ;
    GPIO_InitStructure.GPIO_PuPd  = GPIO_PuPd_UP    ;
    GPIO_InitStructure.GPIO_Speed = GPIO_Speed_25MHz;                         
    GPIO_Init(GPIOD, &GPIO_InitStructure)           ;
    
    GPIO_SetBits  (GPIOD, PLL_NSS );//使能器件ADF4351
    GPIO_ResetBits(GPIOC, PLL_LE  ); 
    GPIO_ResetBits(GPIOC, PLL_DATA);
    GPIO_ResetBits(GPIOC, PLL_CLK);  
}

void adf4351_write_data(unsigned int register_data)
{
	unsigned char i = 0;
	GPIO_ResetBits(GPIOC, PLL_LE) ;  
	delay_us(4)                   ;             
	GPIO_ResetBits(GPIOC, PLL_CLK);
	delay_us(4)                   ;                         
	for(i=0;i<=31;i++)
    { 
        GPIO_ResetBits(GPIOC, PLL_CLK);
        delay_us(2)                   ;
        if(0x80000000 == (register_data&0x80000000))
        {
        	GPIO_SetBits(GPIOC, PLL_DATA);
        }
        else 
        {
        	GPIO_ResetBits(GPIOC, PLL_DATA);
        }
        GPIO_ResetBits(GPIOC, PLL_CLK)  ;
        delay_us(2)                     ;
        GPIO_SetBits(GPIOC, PLL_CLK)    ;
        delay_us(2)                     ;
        GPIO_ResetBits(GPIOC, PLL_CLK)  ; 
        delay_us(2)                     ;
        register_data=register_data << 1;
        delay_us(2)                     ;
    }
    GPIO_ResetBits(GPIOC, PLL_LE) ;  
	delay_us(4)                   ;             
	GPIO_SetBits(GPIOC, PLL_LE)   ;
	delay_us(4)                   ;
	GPIO_ResetBits(GPIOC, PLL_LE) ;
	delay_us(4)                   ;  
	GPIO_ResetBits(GPIOC, PLL_CLK);  	 	 
}


void adf4351_freq_2450init(void)
{
	adf4351_write_data(0x4c8008);
	delay_us(10);
	adf4351_write_data(0x8008041);
	delay_us(10);
	adf4351_write_data(0x60005E42);
	delay_us(10);
	adf4351_write_data(0x4B3);
	delay_us(10);
	adf4351_write_data(0x8800FC);
	delay_us(10);
	adf4351_write_data(0x580005);
	delay_us(10);
}

void Generate_2450MHz_Freq(void)
{
	adf4351_freq_2450init();delay_us(10);
	adf4351_freq_2450init();delay_us(10);
	adf4351_freq_2450init();delay_us(10);
}

void adf4351_freq(unsigned int data_number)
{
	adf4351_write_data(N1_Cdata[data_number]);                                              
	delay_us(10);                                                              
	adf4351_write_data(N2_Cdata[data_number]);                                             
	delay_us(10);                                                              
	adf4351_write_data(0x60005E42);                                            
	delay_us(10);                                                              
	adf4351_write_data(0x4B3);                                                 
 	delay_us(10);                                                              
 	adf4351_write_data(0x8800FC);                                              
	delay_us(10);                                                              
	adf4351_write_data(0x580005);                                              
	delay_us(10);
}	

void set_freq(unsigned int data_number)
{
    if(Freq>MAX_FREQ) Freq=MAX_FREQ;
    if(Freq<MIN_FREQ) Freq=MIN_FREQ;
	  adf4351_freq((Freq-2400)*10);delay_us(10);
	  adf4351_freq((Freq-2400)*10);delay_us(10);
	  adf4351_freq((Freq-2400)*10);delay_us(10);
}	
