YangXiao69/WSPS-325-150K-PEFA/测试/WSPS-325-150K-CEWG-292-V1.0-test/User/bsp/bsp_spiflash/bsp_w25q64.h

#ifndef __BSP_W25Q64_H
#define __BSP_W25Q64_H

#include "stm32f4xx.h"
#include <stdio.h>

/* Private typedef -----------------------------------------------------------*/
#define  W25X16                       0xEF3015     //W25X16
#define  W25Q16                       0xEF4015	   //W25Q16
#define  W25Q64                       0XEF4017     //W25Q64
#define  W25Q128                      0XEF4018     //W25Q128


#define CMD_ADDR_MIN  1000
#define CMD_ADDR_MAX  1950
#define CMD_CNT       950


#define errcnt 950


#define WRT_TIME_CNT 2000



#define SPI_FLASH_PageSize            4096
#define SPI_FLASH_TotalSize           8 * 1024 * 1024    
#define SPI_FLASH_PerWritePageSize    256     //页字节大小
#define SPI_FLASH_RWPageSize          10     //页字节大小
#define SPI_FLASH_Store_ErrNum_Addr   0x0000

/* Private define ------------------------------------------------------------*/
/*命令定义-开头*******************************/
#define W25X_WriteEnable		      0x06 
#define W25X_WriteDisable		      0x04 
#define W25X_ReadStatusReg		      0x05 
#define W25X_WriteStatusReg		      0x01 
#define W25X_ReadData			      0x03 
#define W25X_FastReadData		      0x0B 
#define W25X_FastReadDual		      0x3B 
#define W25X_PageProgram		      0x02 
#define W25X_BlockErase			      0xD8 
#define W25X_SectorErase		      0x20 
#define W25X_ChipErase			      0xC7 
#define W25X_PowerDown			      0xB9 
#define W25X_ReleasePowerDown	      0xAB 
#define W25X_DeviceID			      0xAB 
#define W25X_ManufactDeviceID   	  0x90 
#define W25X_JedecDeviceID		      0x9F 

#define WIP_Flag                  0x01  /* Write In Progress (WIP) flag */
#define Dummy_Byte                0xFF
/*命令定义-结尾*******************************/


/*SPI接口定义-开头****************************/
#define FLASH_SPI                           SPI5
#define FLASH_SPI_CLK                       RCC_APB2Periph_SPI5
#define FLASH_SPI_CLK_INIT                  RCC_APB2PeriphClockCmd

#define FLASH_SPI_SCK_PIN                   GPIO_Pin_7                  
#define FLASH_SPI_SCK_GPIO_PORT             GPIOF                       
#define FLASH_SPI_SCK_GPIO_CLK              RCC_AHB1Periph_GPIOF
#define FLASH_SPI_SCK_PINSOURCE             GPIO_PinSource7
#define FLASH_SPI_SCK_AF                    GPIO_AF_SPI5

#define FLASH_SPI_MISO_PIN                  GPIO_Pin_8                
#define FLASH_SPI_MISO_GPIO_PORT            GPIOF                   
#define FLASH_SPI_MISO_GPIO_CLK             RCC_AHB1Periph_GPIOF
#define FLASH_SPI_MISO_PINSOURCE            GPIO_PinSource8
#define FLASH_SPI_MISO_AF                   GPIO_AF_SPI5

#define FLASH_SPI_MOSI_PIN                  GPIO_Pin_9                
#define FLASH_SPI_MOSI_GPIO_PORT            GPIOF                      
#define FLASH_SPI_MOSI_GPIO_CLK             RCC_AHB1Periph_GPIOF
#define FLASH_SPI_MOSI_PINSOURCE            GPIO_PinSource9
#define FLASH_SPI_MOSI_AF                   GPIO_AF_SPI5

#define FLASH_CS_PIN                        GPIO_Pin_6               
#define FLASH_CS_GPIO_PORT                  GPIOF                     
#define FLASH_CS_GPIO_CLK                   RCC_AHB1Periph_GPIOF

#define SPI_FLASH_CS_LOW()      {FLASH_CS_GPIO_PORT->BSRRH=FLASH_CS_PIN;}
#define SPI_FLASH_CS_HIGH()     {FLASH_CS_GPIO_PORT->BSRRL=FLASH_CS_PIN;}
/*SPI接口定义-结尾****************************/

/*等待超时时间*/
#define SPIT_FLAG_TIMEOUT         ((uint32_t)0x1000)
#define SPIT_LONG_TIMEOUT         ((uint32_t)(10 * SPIT_FLAG_TIMEOUT))


#define FLASHReadWriteSize 		 4096
#define NumByteToReadWrite 		 23

void SPI_FLASH_Init(void);
void SPI_FLASH_SectorErase(u32 SectorAddr);
void SPI_FLASH_BulkErase(void);
void SPI_FLASH_PageWrite(u8* pBuffer, u32 WriteAddr, u16 NumByteToWrite);
void SPI_FLASH_BufferWrite(u8* pBuffer, u32 WriteAddr, u16 NumByteToWrite);
void SPI_FLASH_BufferRead(u8* pBuffer, u32 ReadAddr, u16 NumByteToRead);
u32 SPI_FLASH_ReadID(void);
u32 SPI_FLASH_ReadDeviceID(void);
void SPI_FLASH_StartReadSequence(u32 ReadAddr);
void SPI_Flash_PowerDown(void);
void SPI_Flash_WAKEUP(void);


void wtCmdToFlash(u16 num,u16 code, u16 cmdvalue, u8 *time);




u8 SPI_FLASH_ReadByte(void);
u8 SPI_FLASH_SendByte(u8 byte);
u16 SPI_FLASH_SendHalfWord(u16 HalfWord);
void SPI_FLASH_WriteEnable(void);
void SPI_FLASH_WaitForWriteEnd(void);
void wtErrToFlash(u16 num,u16 code,u8 time[5]);
void rdErrFromFlash(u16 num,uint8_t Rx_Buffer[10]);
void sf_EraseSector(uint32_t _uiSectorAddr);
void sf_ReadBuffer(uint8_t * _pBuf, uint32_t _uiReadAddr, uint32_t _uiSize);
uint8_t sf_WriteBuffer(uint8_t* _pBuf, uint32_t _uiWriteAddr, uint16_t _usWriteSize);


void rdCmdFromFlash(u16 num,uint8_t *Rx_Buffer);

void Empty_TimeLog(void);
void CalRunTime(void);
void SaveRunTime(void);
void GetTotalRunTime(void);

void Get_StoreCMD_Num(void);
void Get_StoreException_Num(void);
void Get_ExceptionCMD_Num(void);



#endif  
