YangXiao69/WSPS-325-150K-PEFA/测试/WSPS-325-150K-CEWG-292-V1.0-test/User/bsp/bsp.h

#ifndef  __BSP_H
#define  __BSP_H



#include "./bsp_adc/bsp_adc.h"
#include "./bsp_adf4351/bsp_adf4351.h"
#include "./bsp_dac/bsp_dac.h"
#include "./bsp_ds18b20/bsp_ds18b20.h"
#include "./bsp_eeprom/bsp_i2cee.h" 
#include "./bsp_led/bsp_led.h"
#include "./bsp_timer/bsp_general_timer.h"
#include "./bsp_usart/bsp_usart.h"
#include "./bsp_spiflash/bsp_w25q64.h"





void delay_us(uint16_t nCount);
void delay_ms(uint16_t nCount);


void Bsp_Inits(void);




#endif
